uvic-auvic/Mechanical-Team/lobsta_concept_CAD/auv_assemblies/top_lid_assembly.sldasm

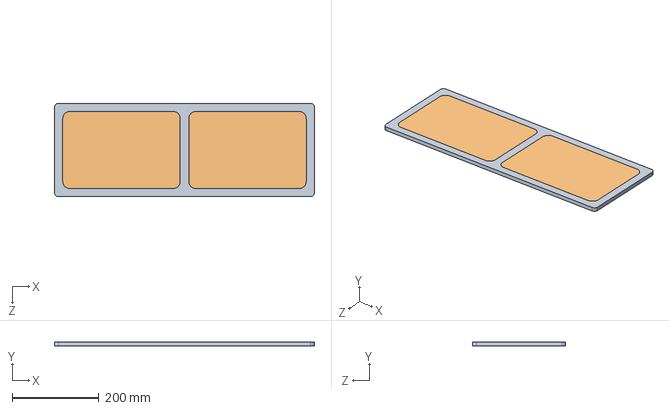
[picture p14: CAD file, 2020-06-30]
lobsta_concept_CAD/auv_assemblies/top_lid_assembly.sldasm
599.0 x 9.00 x 215.4 mm
lid_rectangular
Lid_window x 2
