uvic-auvic/Mechanical-Team/lobsta_concept_CAD/auv_assemblies/front_plate_assembly.sldasm

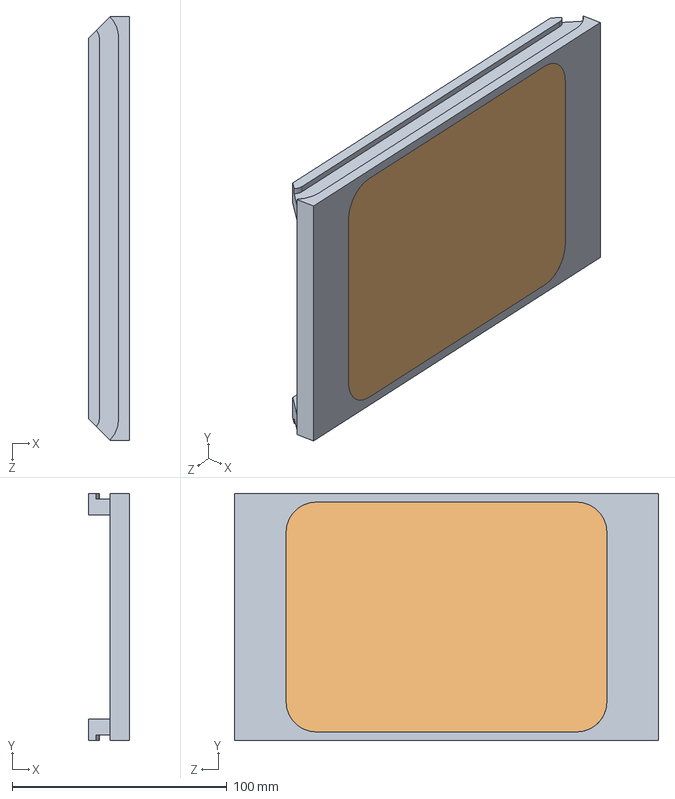
[picture p18: CAD file, 2020-06-30]
lobsta_concept_CAD/auv_assemblies/front_plate_assembly.sldasm
19.0 x 115.0 x 197.4 mm
front_plate
front_window_single
