uvic-auvic/Mechanical-Team/Final Assembly_POLARIS/Hub_bearing_assembly.SLDASM

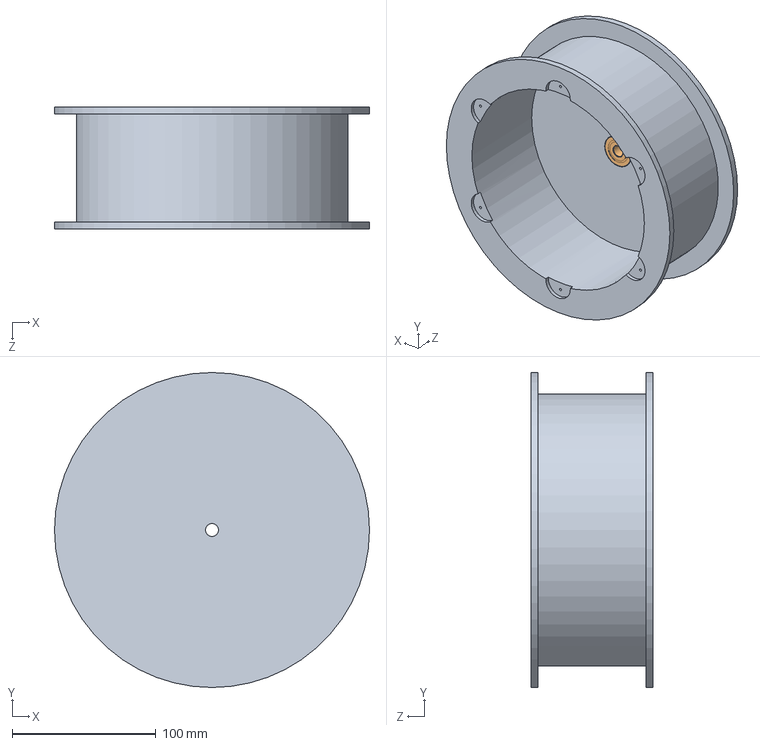
[picture p19: CAD file, 2020-06-30]
Final Assembly_POLARIS/Hub_bearing_assembly.SLDASM
219.0 x 219.0 x 85.0 mm
Hub
Outer_shaft_bearing
