uvic-auvic/Mechanical-Team/lobsta_concept_CAD/lobsta_shell_assem.SLDASM

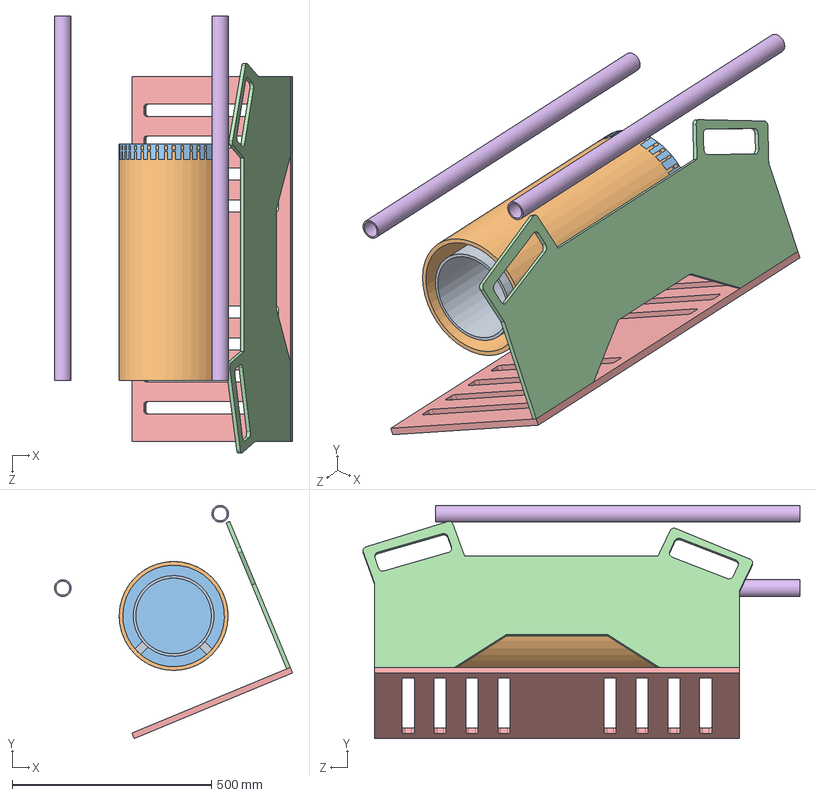
[picture p20: CAD file, 2020-01-29]
lobsta_concept_CAD/lobsta_shell_assem.SLDASM
597.3 x 584.7 x 1095.7 mm
inner_main_shell
outer_main_shell
cap
side_frame
flat_frame
Pontoon x 2
