uvic-auvic/Mechanical-Team/frame/demonstration/SubASSEM_TopBottomRail.SLDASM

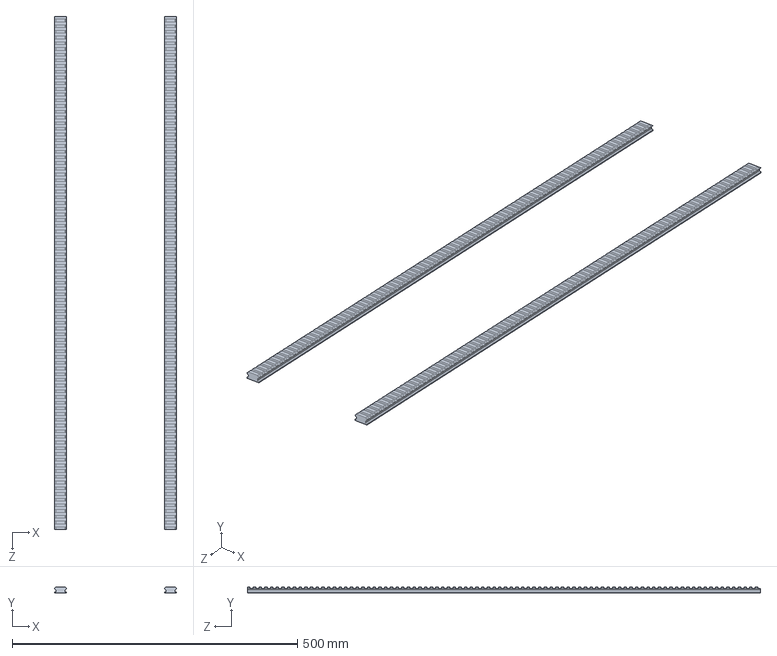
[picture p21: CAD file, 2020-06-30]
frame/demonstration/SubASSEM_TopBottomRail.SLDASM
214.0 x 11.2 x 900.0 mm
PART_PicRail x 2
