uvic-auvic/Mechanical-Team/lobsta_concept_CAD/auv_assemblies/bottom_lid_assembly.sldasm

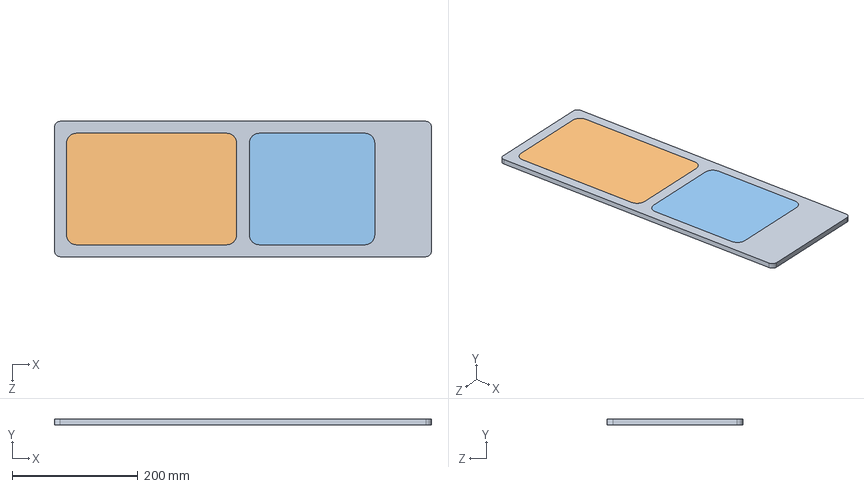
[picture p22: CAD file, 2020-06-30]
lobsta_concept_CAD/auv_assemblies/bottom_lid_assembly.sldasm
599.0 x 9.00 x 215.4 mm
lid_rectangular_bottom
Lid_window
lid_window_bottom_small
