uvic-auvic/Mechanical-Team/lobsta_concept_CAD/outer_main_shell.SLDPRT

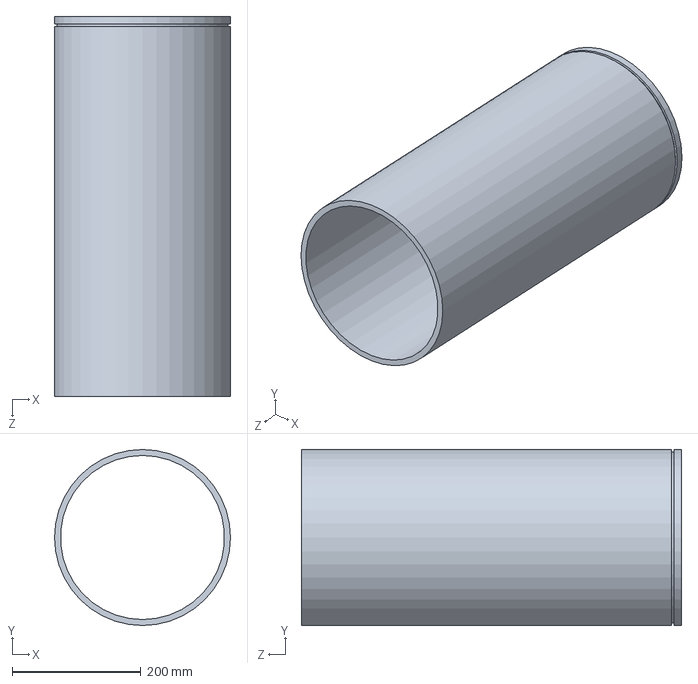
[picture p23: CAD file, 2020-01-29]
lobsta_concept_CAD/outer_main_shell.SLDPRT
273.1 x 273.1 x 590.0 mm
