uvic-auvic/Mechanical-Team/lobsta_concept_CAD/auv_assemblies/side_plate_assembly.sldasm

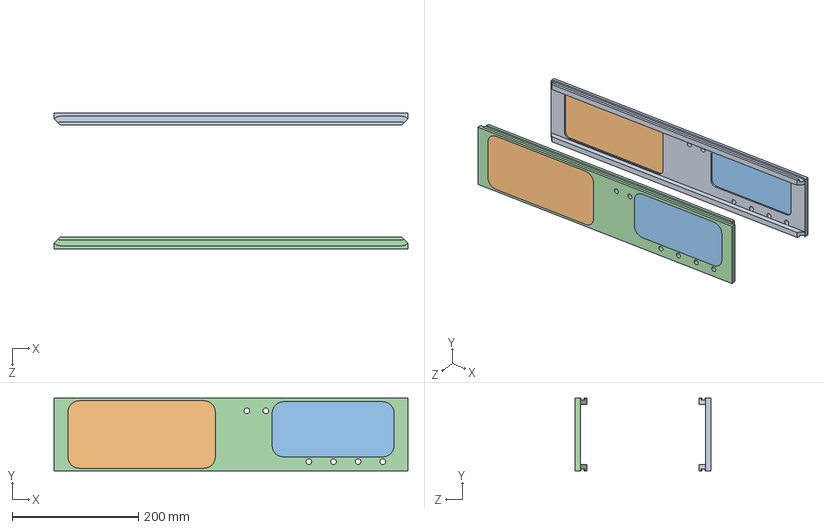
[picture p24: CAD file, 2020-05-26]
lobsta_concept_CAD/auv_assemblies/side_plate_assembly.sldasm
561.0 x 115.0 x 215.4 mm
side_plate
side_window_large x 2
side_window_small x 2
Mirrorside_plate
