uvic-auvic/Mechanical-Team/Final Assembly_POLARIS/Planet_Assembly.SLDASM

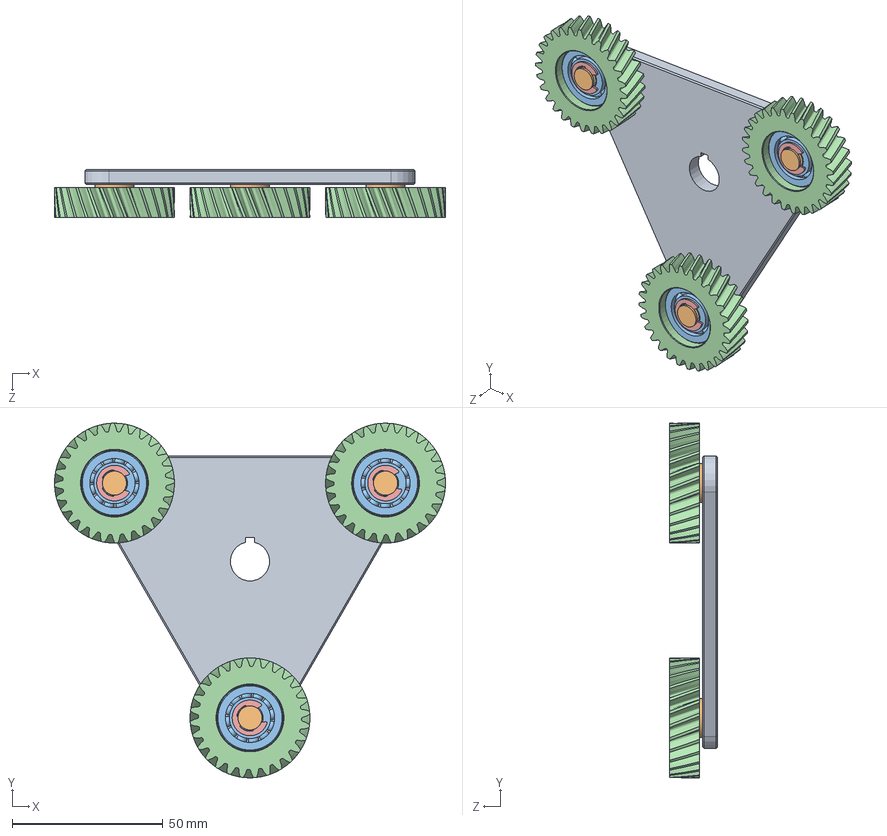
[picture p25: CAD file, 2020-06-30]
Final Assembly_POLARIS/Planet_Assembly.SLDASM
129.6 x 117.6 x 16.0 mm
Carrier
planetshaftMECH360 x 3
Planet Bearing x 3
Planet 28t x 3
98543A114_SIDE-MOUNT EXTERNAL RETAINING RING E-STYLE x 3
