uvic-auvic/Mechanical-Team/Final Assembly_POLARIS/Motor_assembly_rev1.SLDASM

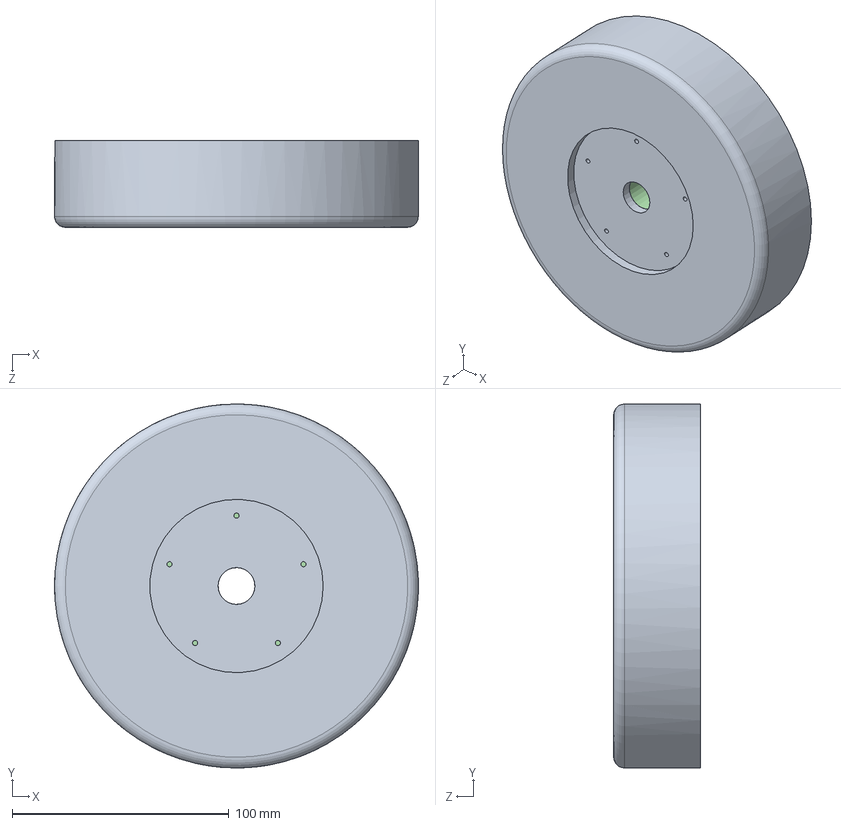
[picture p26: CAD file, 2020-06-30]
Final Assembly_POLARIS/Motor_assembly_rev1.SLDASM
168.0 x 168.0 x 40.0 mm
Motor_cover_rev1
Motor_stator
Motor_circuit_board
Motor_Rotor_rev1
