uvic-auvic/Mechanical-Team/lobsta_concept_CAD/Camera Housing/Camera_Housing_Assy.SLDASM

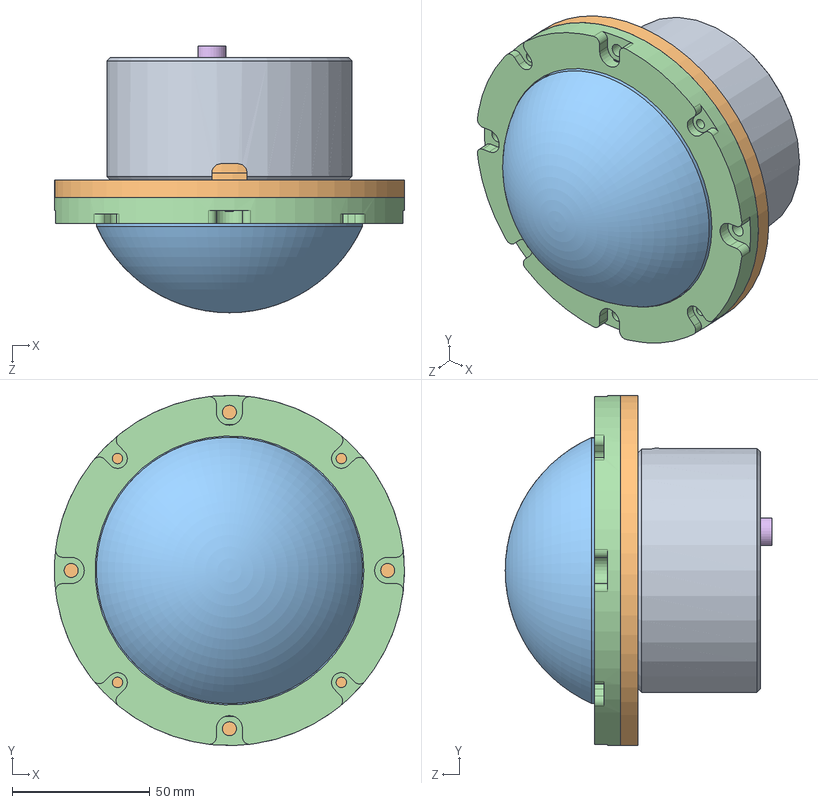
[picture p27: CAD file, 2020-03-10]
lobsta_concept_CAD/Camera Housing/Camera_Housing_Assy.SLDASM
127.0 x 127.0 x 96.7 mm
Camera_Housing
auv01_camera_hull_front_cap_videoray
auv01_camera_dome_videoray
auv01_camera_hull_lens_holder_dome_videoray
Bottom Facing Camera Mount
Maybe Screw
Test Camera (2)
Vertical Stopper
