uvic-auvic/Mechanical-Team/Final Assembly_POLARIS/Sun_Motor_Assembly.SLDASM

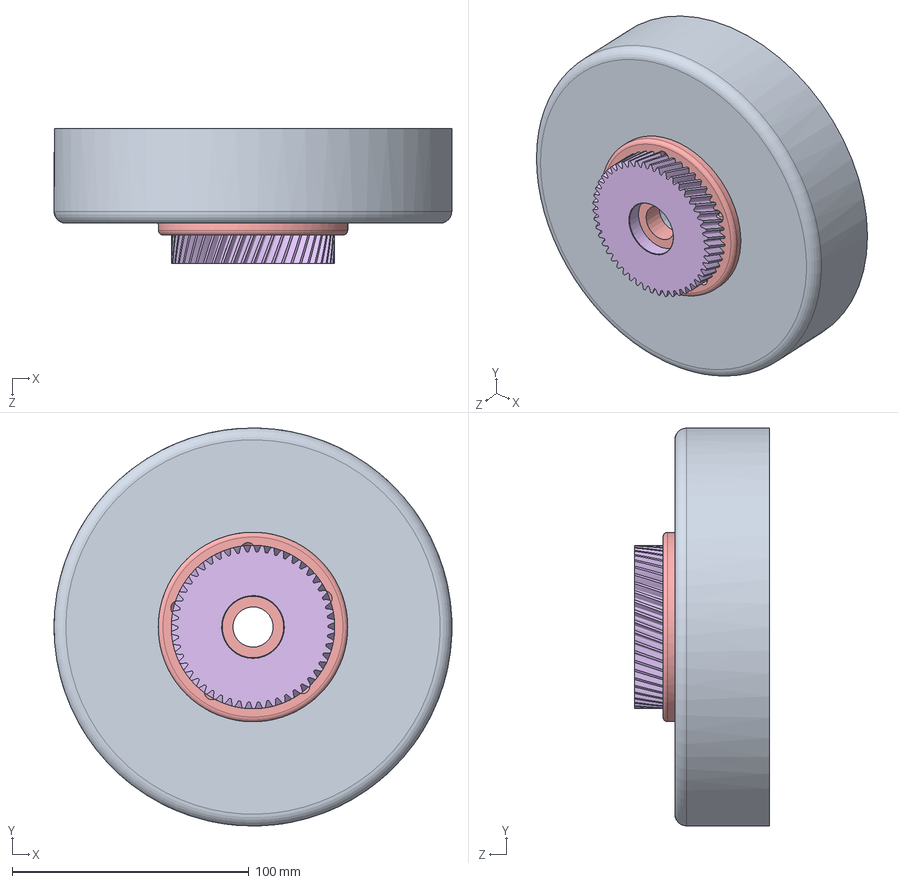
[picture p28: CAD file, 2020-06-30]
Final Assembly_POLARIS/Sun_Motor_Assembly.SLDASM
168.0 x 168.0 x 57.0 mm
Motor_cover_rev1
Motor_stator
Motor_circuit_board
Motor_Rotor_rev1
Attachment Detail
Sun 50t
