uvic-auvic/Mechanical-Team/Final Assembly_POLARIS/Sun_gear_motor_assembly.SLDASM

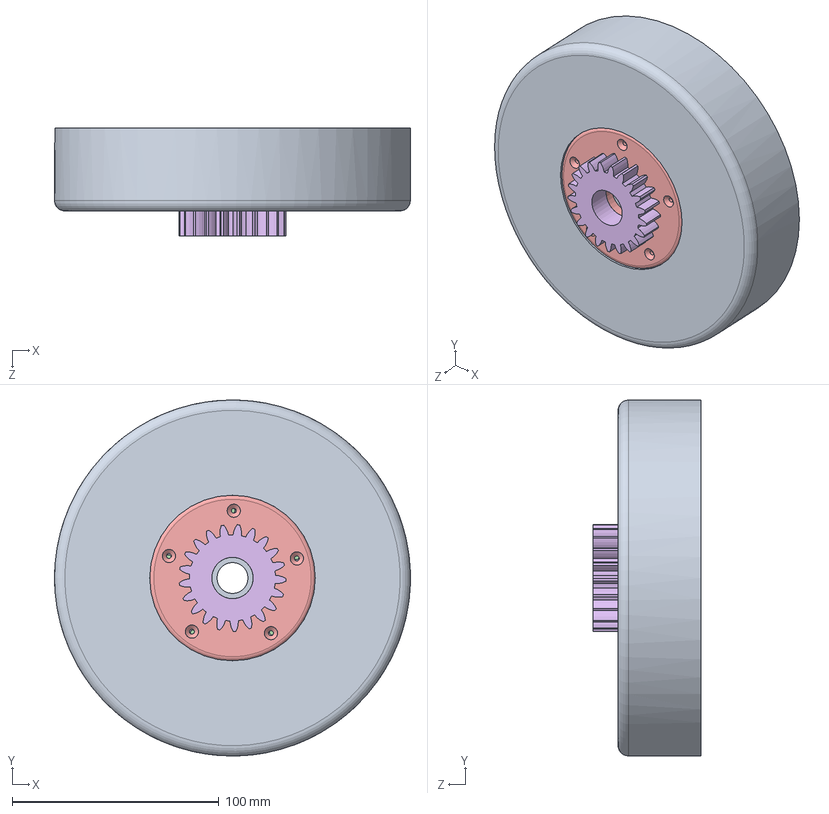
[picture p29: CAD file, 2020-06-30]
Final Assembly_POLARIS/Sun_gear_motor_assembly.SLDASM
172.0 x 172.0 x 52.0 mm
Motor_cover_rev1
Motor_stator
Motor_circuit_board
Motor_Rotor_rev1
Attachment Detail
spur gear_iso
