uvic-auvic/Mechanical-Team/Final Assembly_POLARIS/Sun Gear Attachment.SLDASM

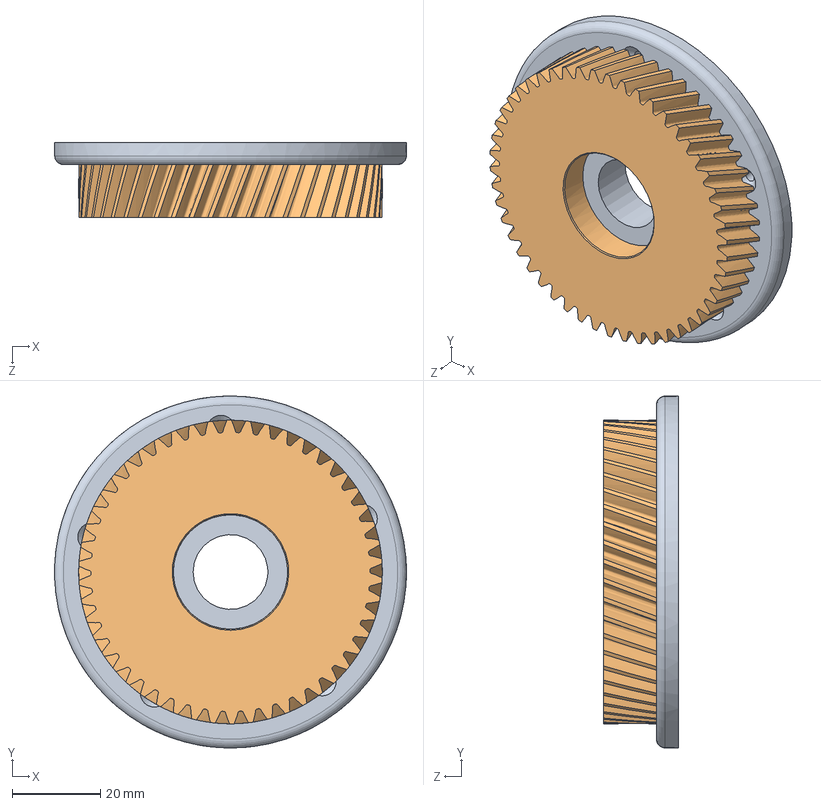
[picture p30: CAD file, 2020-06-30]
Final Assembly_POLARIS/Sun Gear Attachment.SLDASM
80.0 x 80.0 x 17.0 mm
Attachment Detail
Sun 50t
