uvic-auvic/Mechanical-Team/Final Assembly_POLARIS/Planet Gear Assembly.SLDASM

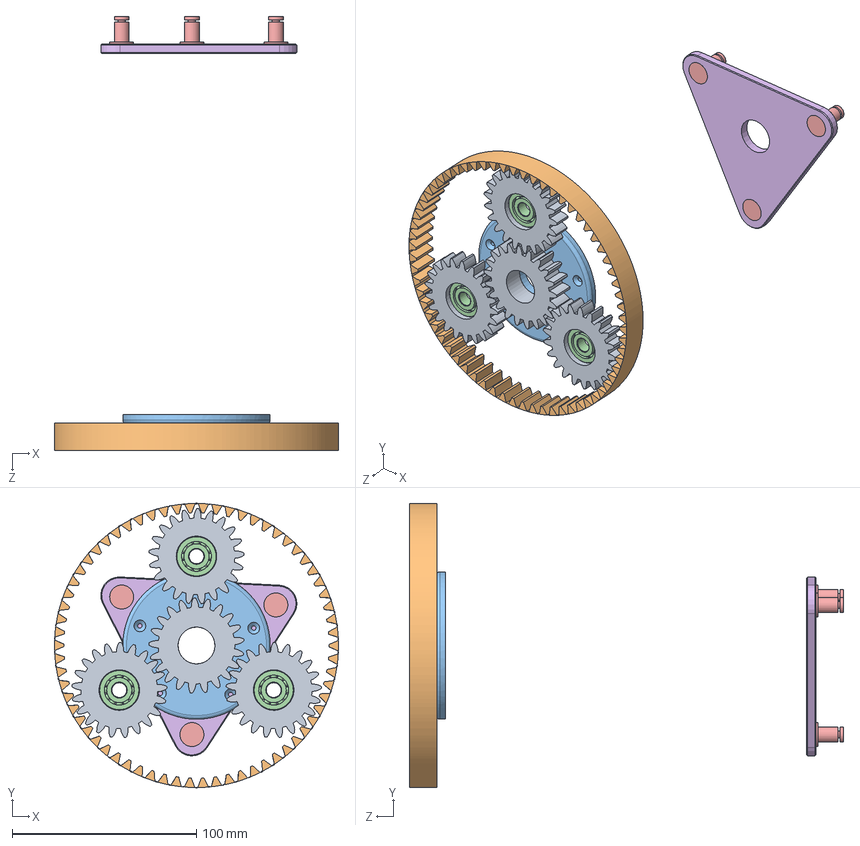
[picture p31: CAD file, 2020-06-30]
Final Assembly_POLARIS/Planet Gear Assembly.SLDASM
154.1 x 154.2 x 235.6 mm
spur gear_iso x 4
internal spur gear_iso
Attachment Detail
5972K910_BALL BEARING x 3
planetshaftMECH360 x 3
Carrier
