uvic-auvic/Mechanical-Team/Final Assembly_POLARIS/Complete_Assem.SLDASM

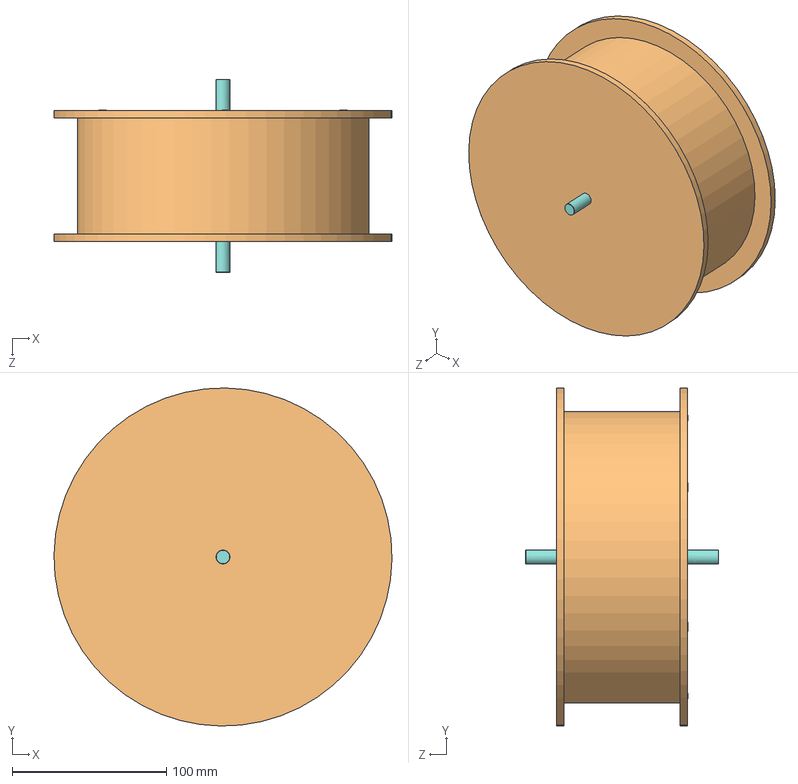
[picture p32: CAD file, 2020-06-30]
Final Assembly_POLARIS/Complete_Assem.SLDASM
219.0 x 219.0 x 125.0 mm
Carrier
planetshaftMECH360 x 3
Planet Bearing x 3
Planet 28t x 3
98543A114_SIDE-MOUNT EXTERNAL RETAINING RING E-STYLE x 3
Ring 106t Left Helix
Sun 50t
Clutch
Sun_bearing
shaftMECH360
Screws x 5
