uvic-auvic/Mechanical-Team/Blue-Robotics Mounts/Thruster Front Mount.SLDPRT

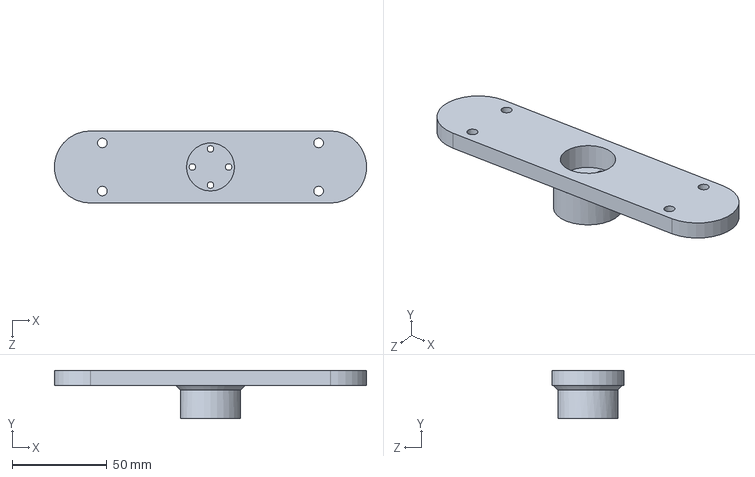
[picture p33: CAD file, 2019-07-23]
Blue-Robotics Mounts/Thruster Front Mount.SLDPRT
164.9 x 25.4 x 38.1 mm
