uvic-auvic/Mechanical-Team/Final Assembly_POLARIS/Motor_stator.SLDPRT

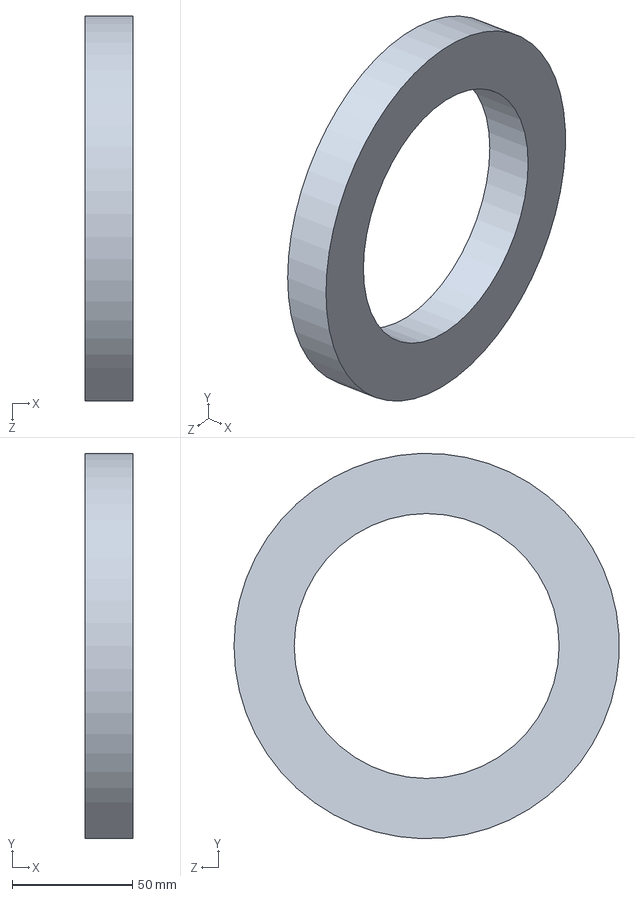
[picture p34: CAD file, 2020-06-30]
Final Assembly_POLARIS/Motor_stator.SLDPRT
20.0 x 159.9 x 159.9 mm
