uvic-auvic/Mechanical-Team/Kill Switch/top key v4.SLDPRT

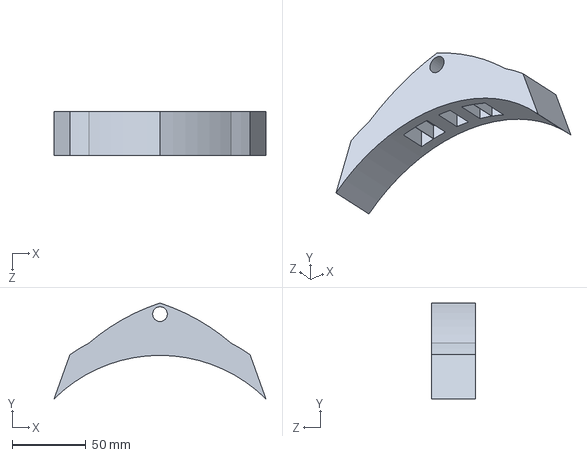
[picture p35: CAD file, 2019-07-21]
Kill Switch/top key v4.SLDPRT
143.7 x 65.1 x 30.0 mm
