uvic-auvic/Mechanical-Team/lobsta_concept_CAD/Ball Dropper/Top Bottom cap.SLDPRT

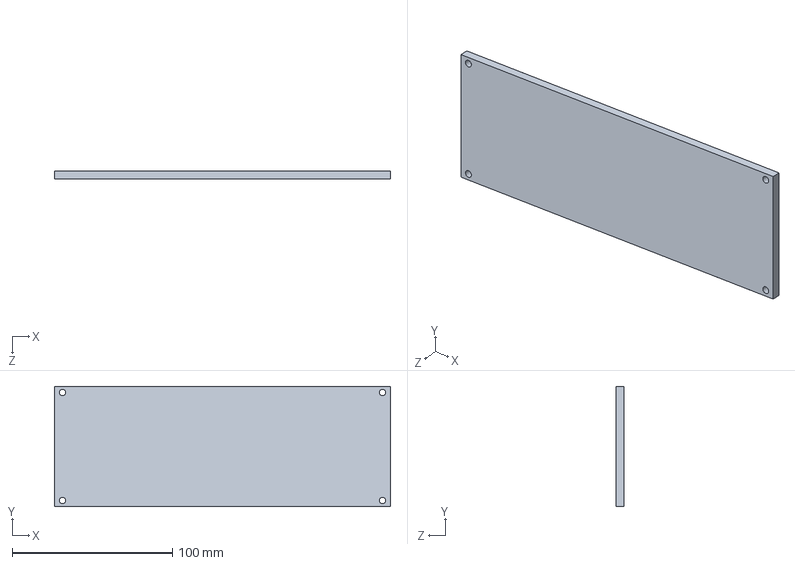
[picture p36: CAD file, 2020-06-09]
lobsta_concept_CAD/Ball Dropper/Top Bottom cap.SLDPRT
210.0 x 75.0 x 5.00 mm
