uvic-auvic/Mechanical-Team/lobsta_concept_CAD/battery assembly/cap_remove.SLDPRT

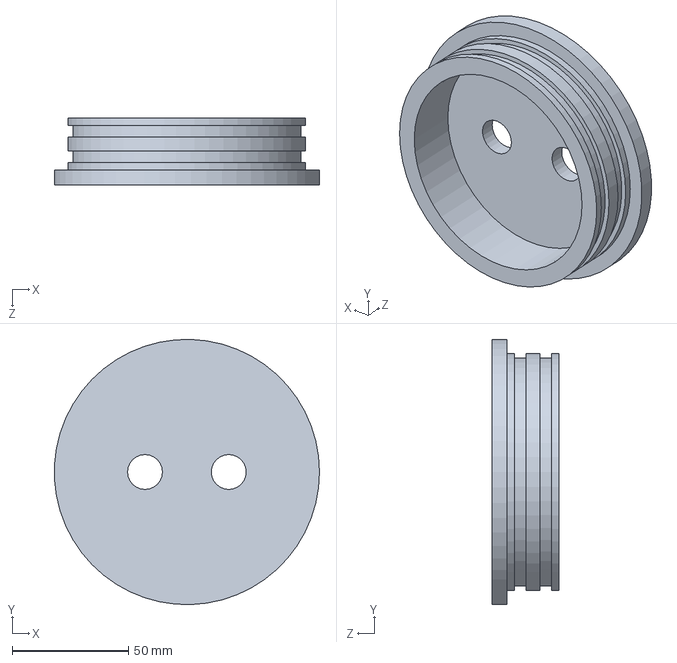
[picture p37: CAD file, 2020-02-05]
lobsta_concept_CAD/battery assembly/cap_remove.SLDPRT
113.9 x 113.9 x 28.7 mm
