uvic-auvic/Mechanical-Team/lobsta_concept_CAD/battery/XT60 Buchse.SLDPRT

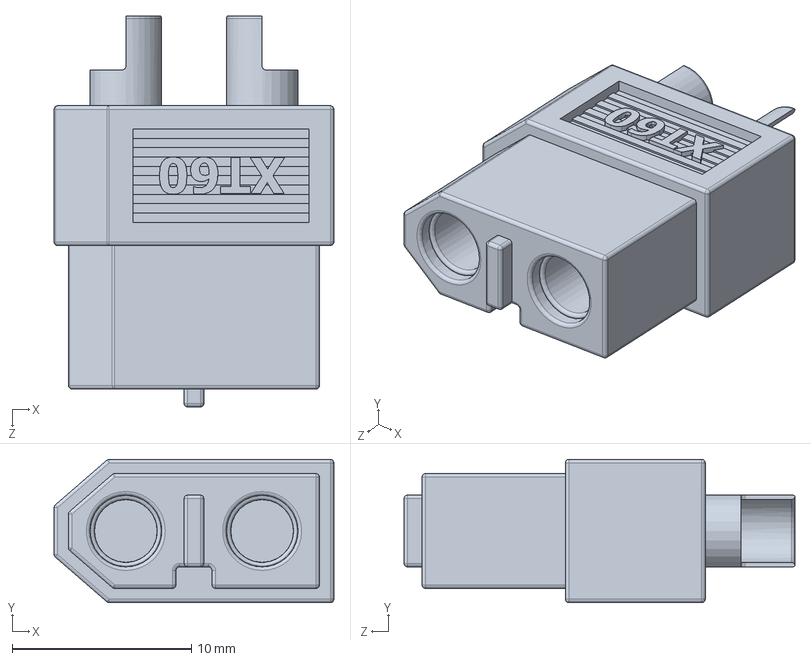
[picture p38: CAD file, 2020-03-18]
lobsta_concept_CAD/battery/XT60 Buchse.SLDPRT
15.6 x 8.00 x 21.8 mm
