uvic-auvic/Mechanical-Team/lobsta_concept_CAD/Camera Housing/Vertical Stopper.SLDPRT

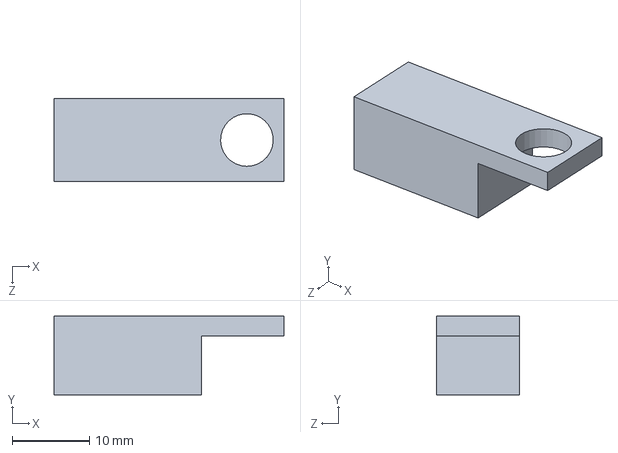
[picture p39: CAD file, 2020-03-10]
lobsta_concept_CAD/Camera Housing/Vertical Stopper.SLDPRT
29.7 x 10.2 x 10.7 mm
