uvic-auvic/Mechanical-Team/lobsta_concept_CAD/hydrophone/HydrophoneLasrecut.SLDPRT

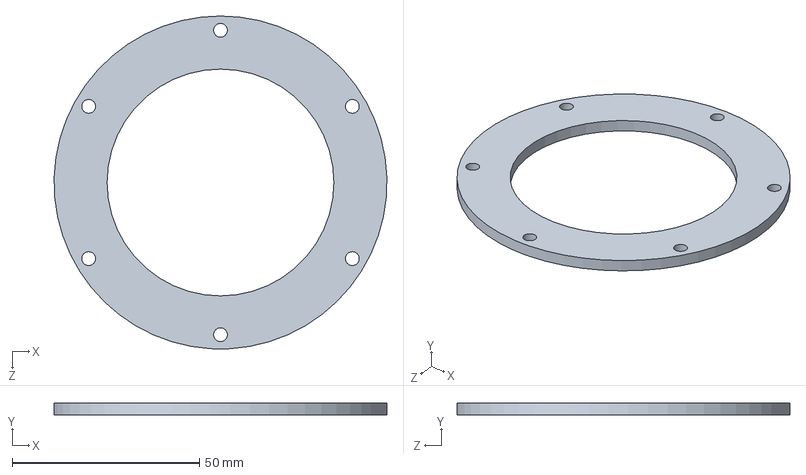
[picture p40: CAD file, 2020-06-30]
lobsta_concept_CAD/hydrophone/HydrophoneLasrecut.SLDPRT
88.9 x 3.17 x 88.9 mm
