uvic-auvic/Mechanical-Team/Mockup Drawings/square_sub/thruster.SLDPRT

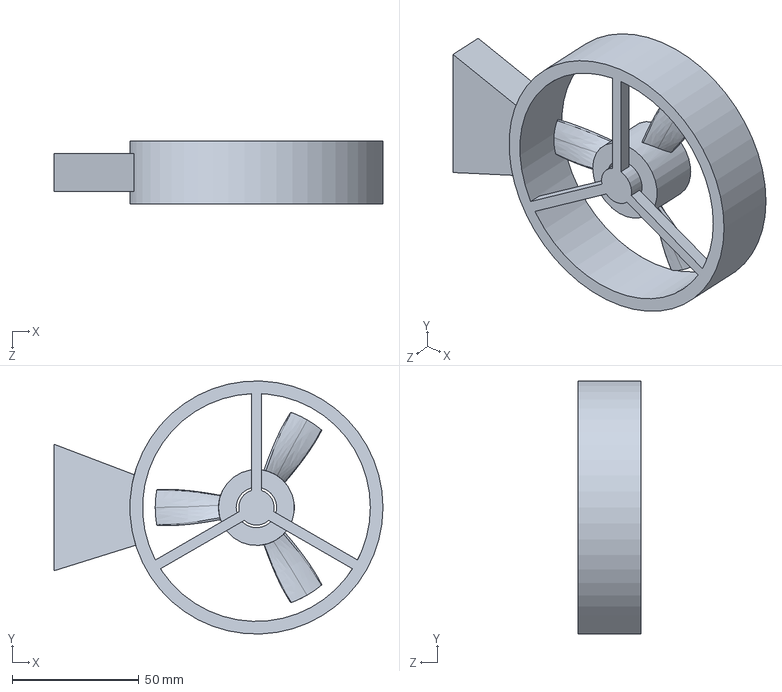
[picture p41: CAD file, 2019-10-25]
Mockup Drawings/square_sub/thruster.SLDPRT
130.0 x 99.9 x 25.0 mm
