uvic-auvic/Mechanical-Team/Torpedos/torpedo.SLDPRT

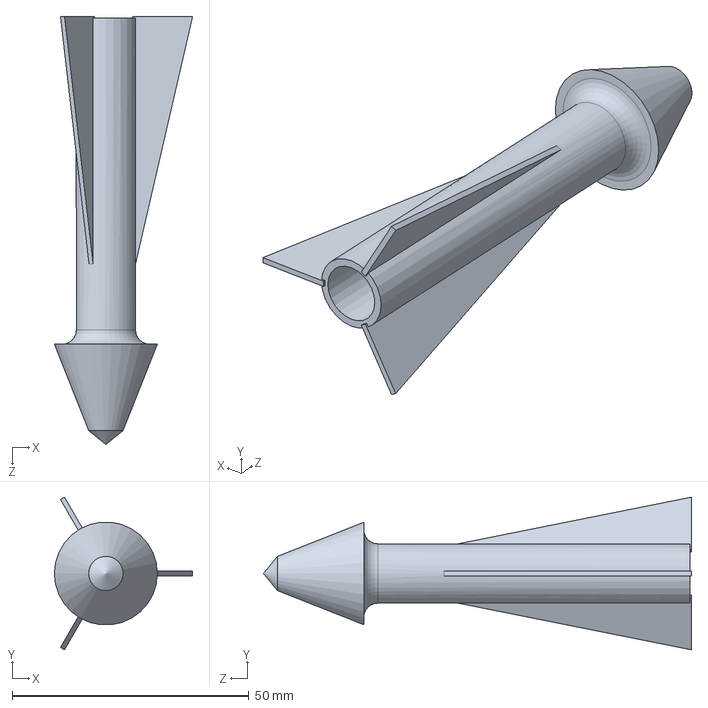
[picture p42: CAD file, 2020-06-09]
Torpedos/torpedo.SLDPRT
29.2 x 32.2 x 90.3 mm
