uvic-auvic/Mechanical-Team/Blue-Robotics Mounts/Thruster Mount.SLDPRT

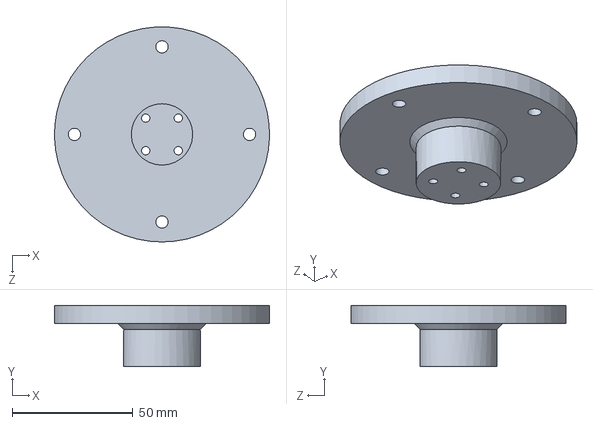
[picture p43: CAD file, 2019-07-18]
Blue-Robotics Mounts/Thruster Mount.SLDPRT
88.9 x 25.4 x 88.8 mm
