uvic-auvic/Mechanical-Team/Final Assembly_POLARIS/ShaftSleeve.SLDPRT

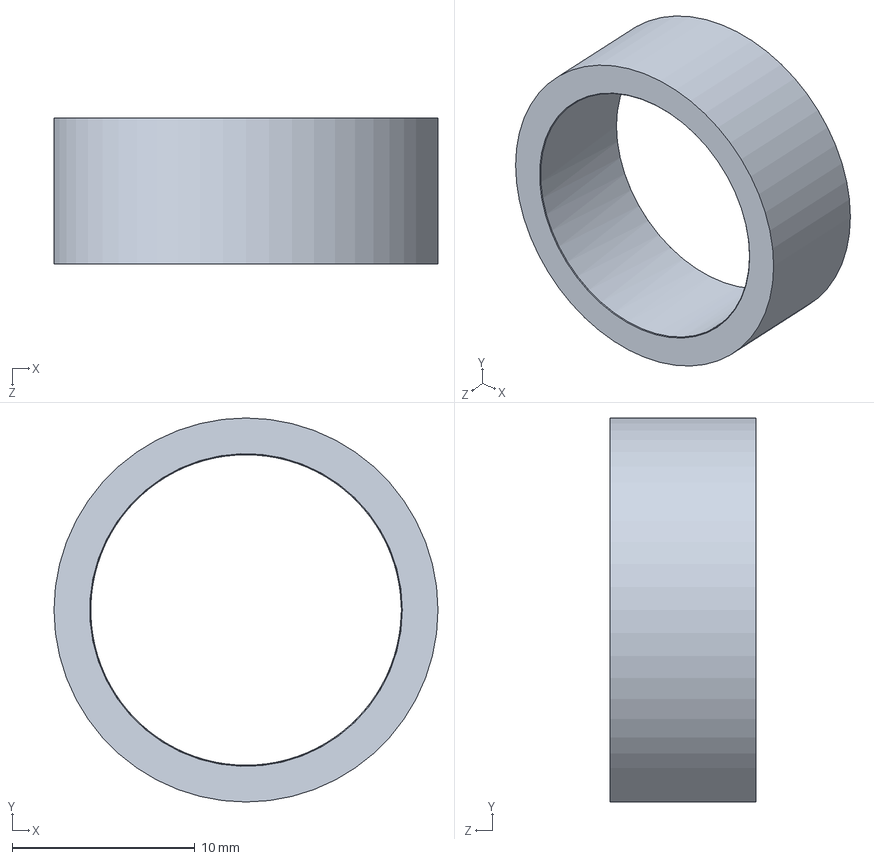
[picture p44: CAD file, 2020-06-30]
Final Assembly_POLARIS/ShaftSleeve.SLDPRT
21.0 x 21.0 x 8.00 mm
