uvic-auvic/Mechanical-Team/frame/demonstration/stand.SLDPRT

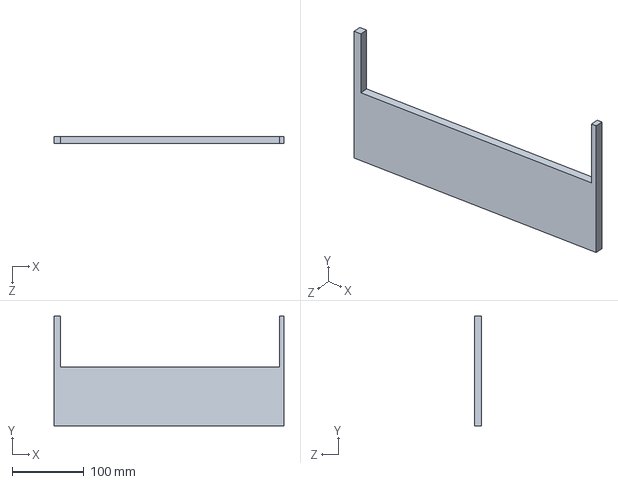
[picture p45: CAD file, 2020-06-30]
frame/demonstration/stand.SLDPRT
320.0 x 152.4 x 10.0 mm
