uvic-auvic/Mechanical-Team/Kill Switch/kill switch bottom.SLDPRT

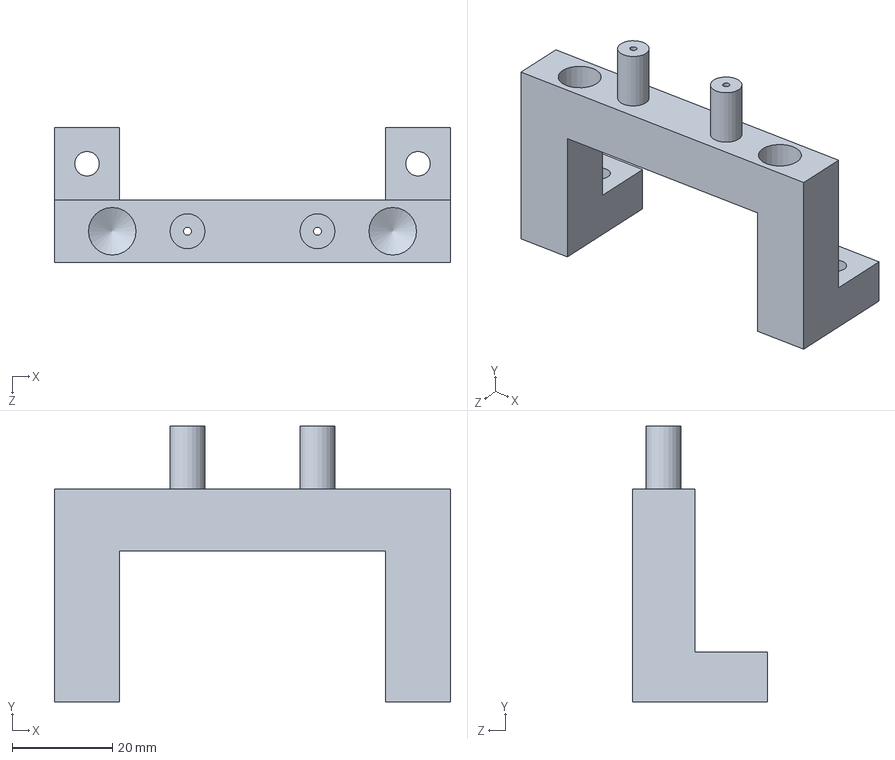
[picture p46: CAD file, 2019-07-21]
Kill Switch/kill switch bottom.SLDPRT
79.2 x 55.1 x 27.0 mm
