uvic-auvic/Mechanical-Team/lobsta_concept_CAD/auv_assemblies/front_window_single.sldprt

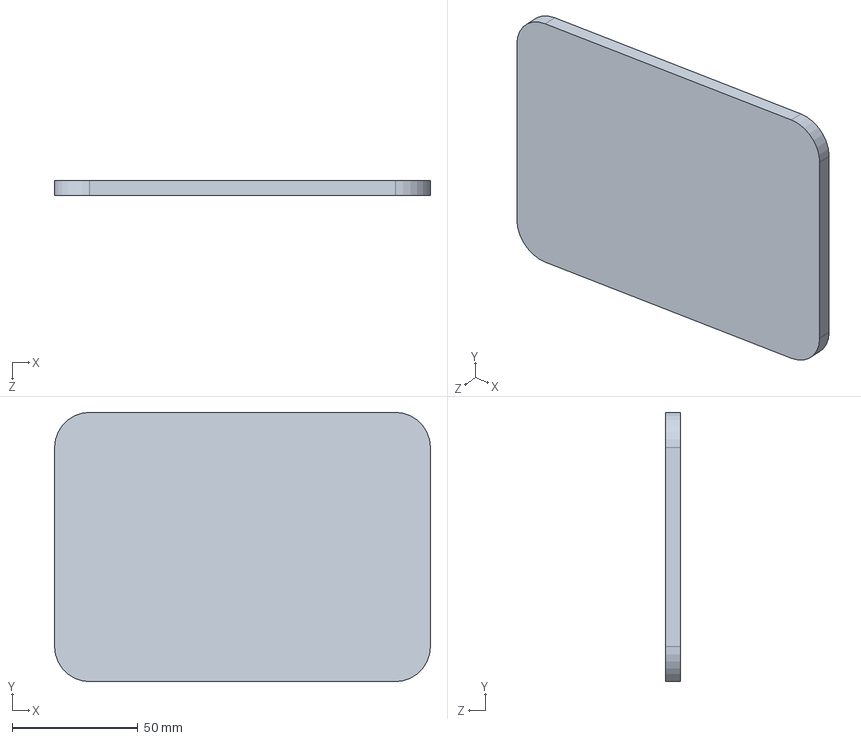
[picture p47: CAD file, 2020-06-30]
lobsta_concept_CAD/auv_assemblies/front_window_single.sldprt
149.4 x 107.0 x 6.00 mm
