uvic-auvic/Mechanical-Team/lobsta_concept_CAD/Ball Dropper/Side Plate.SLDPRT

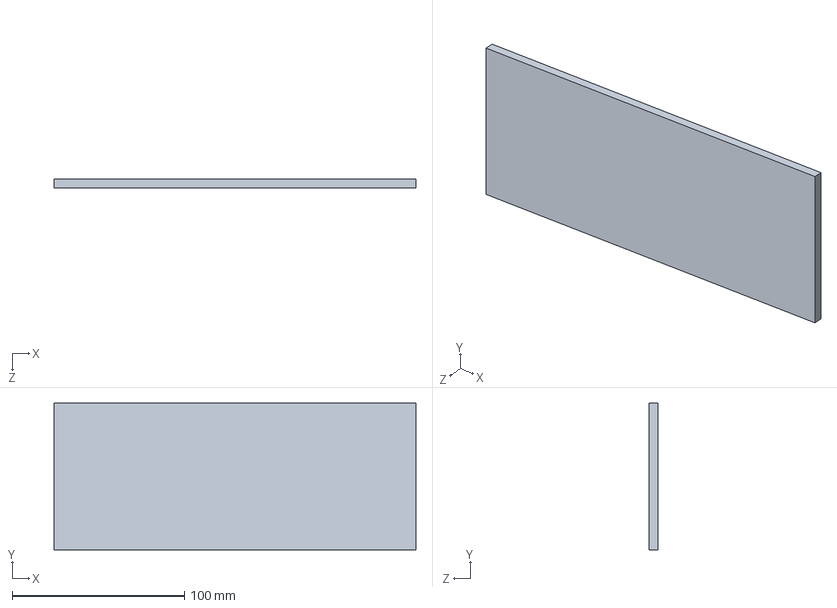
[picture p48: CAD file, 2020-06-09]
lobsta_concept_CAD/Ball Dropper/Side Plate.SLDPRT
210.0 x 85.0 x 5.00 mm
