uvic-auvic/Mechanical-Team/lobsta_concept_CAD/battery assembly/housing.SLDPRT

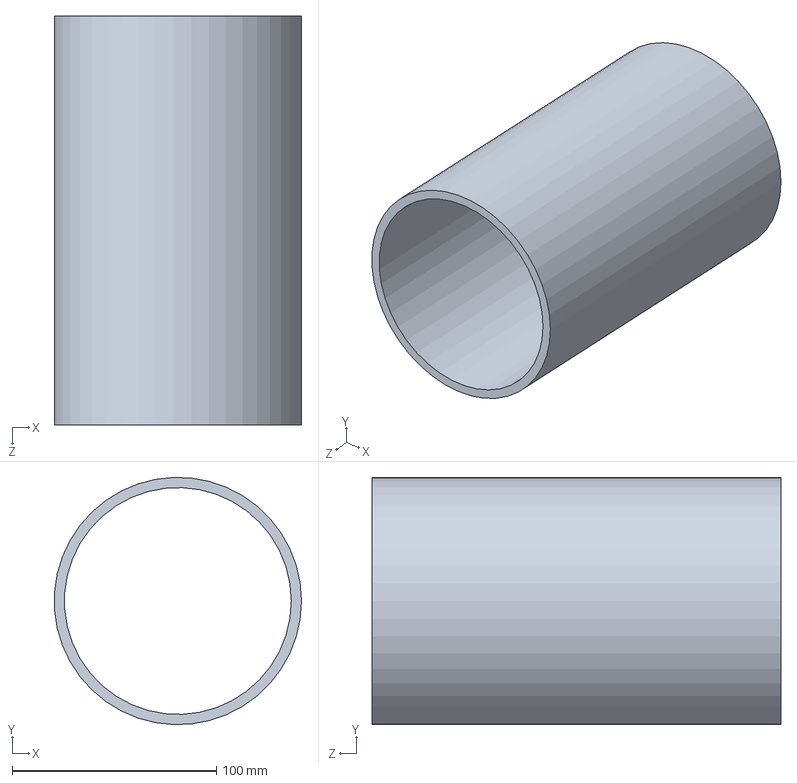
[picture p49: CAD file, 2020-02-05]
lobsta_concept_CAD/battery assembly/housing.SLDPRT
120.8 x 120.9 x 200.0 mm
