uvic-auvic/Mechanical-Team/lobsta_concept_CAD/Camera Housing/Camera_Housing.SLDPRT

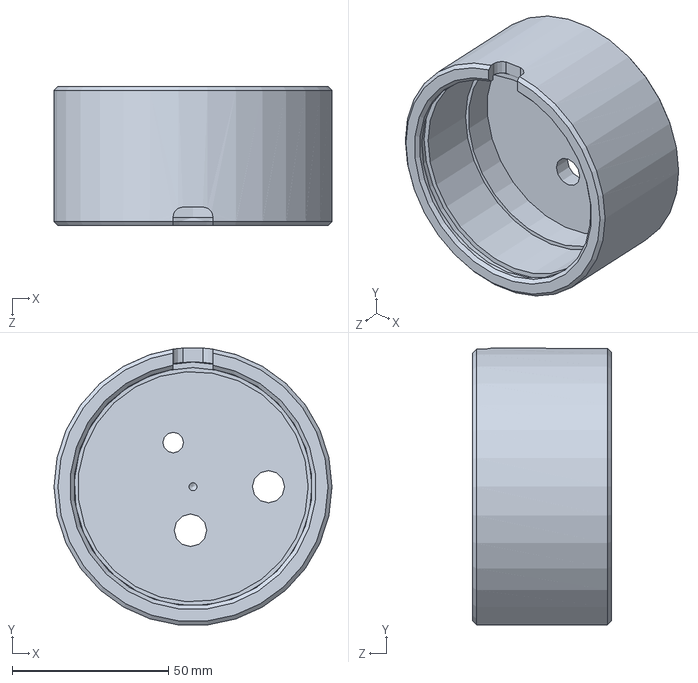
[picture p50: CAD file, 2020-03-10]
lobsta_concept_CAD/Camera Housing/Camera_Housing.SLDPRT
88.9 x 88.5 x 44.5 mm
