uvic-auvic/Mechanical-Team/lobsta_concept_CAD/end_housing.SLDPRT

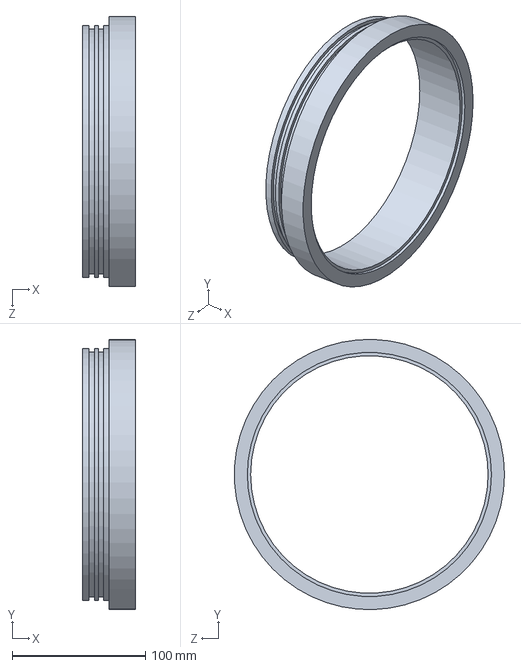
[picture p51: CAD file, 2020-02-05]
lobsta_concept_CAD/end_housing.SLDPRT
40.0 x 202.5 x 202.4 mm
