uvic-auvic/Mechanical-Team/lobsta_concept_CAD/hydrophone/HydrophoneBoard.SLDPRT

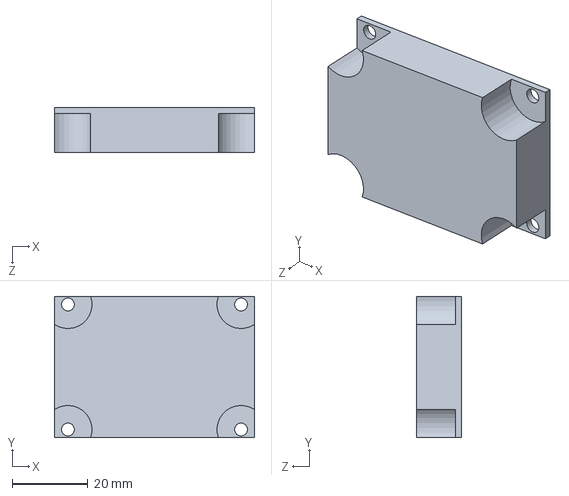
[picture p52: CAD file, 2020-03-03]
lobsta_concept_CAD/hydrophone/HydrophoneBoard.SLDPRT
52.8 x 37.3 x 11.9 mm
