uvic-auvic/Mechanical-Team/lobsta_concept_CAD/solenoid_valve/Solenoid Bracket REV2.SLDPRT

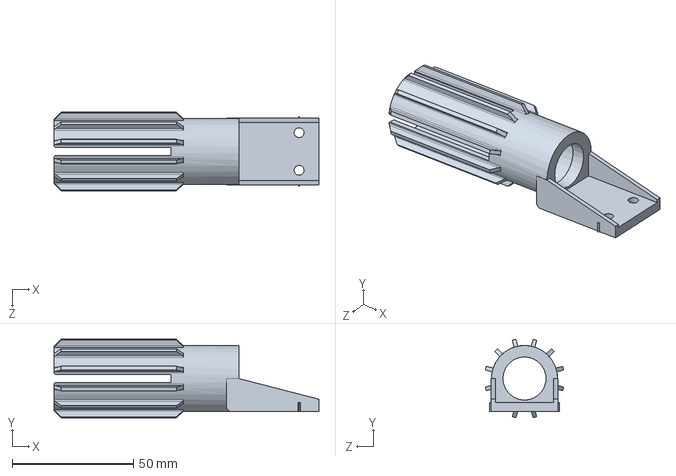
[picture p53: CAD file, 2020-02-08]
lobsta_concept_CAD/solenoid_valve/Solenoid Bracket REV2.SLDPRT
109.2 x 32.4 x 32.4 mm
