uvic-auvic/Mechanical-Team/lobsta_concept_CAD/thrusters/thruster_bracket.sldprt

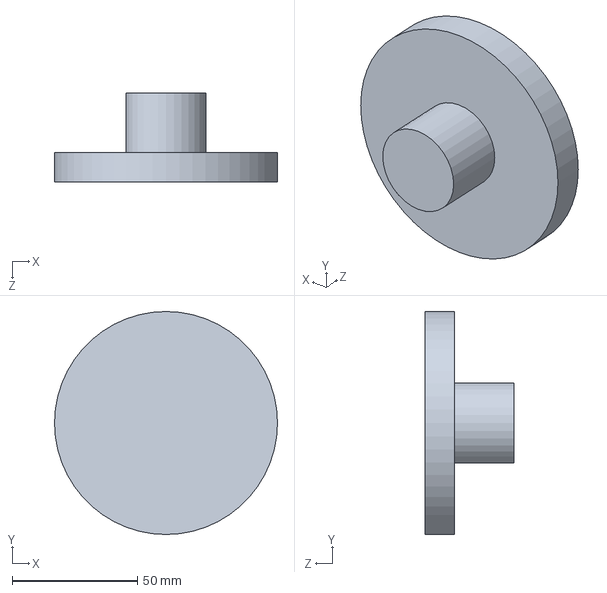
[picture p54: CAD file, 2020-03-03]
lobsta_concept_CAD/thrusters/thruster_bracket.sldprt
89.0 x 89.0 x 35.5 mm
