uvic-auvic/Mechanical-Team/lobsta_concept_CAD/usb_hub/USB-holder-box-v4.SLDPRT

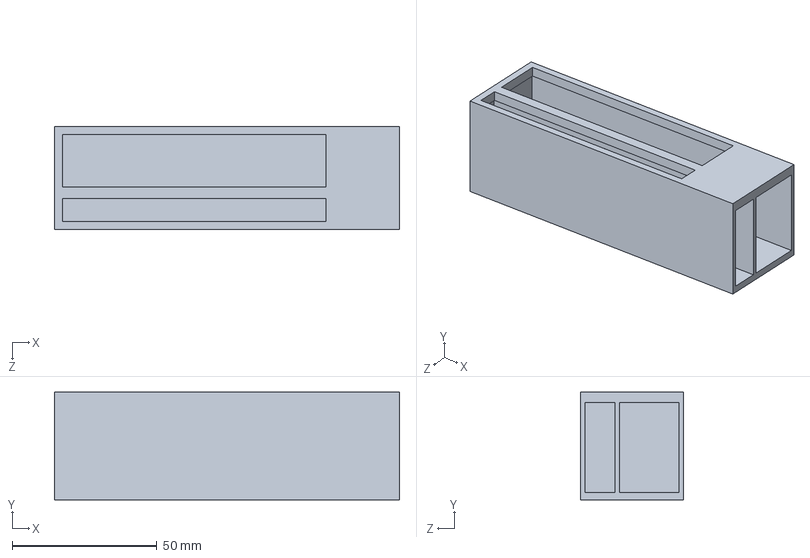
[picture p55: CAD file, 2020-03-18]
lobsta_concept_CAD/usb_hub/USB-holder-box-v4.SLDPRT
119.4 x 37.3 x 35.6 mm
