uvic-auvic/Mechanical-Team/Mockup Drawings/square_sub/side_plate.SLDPRT

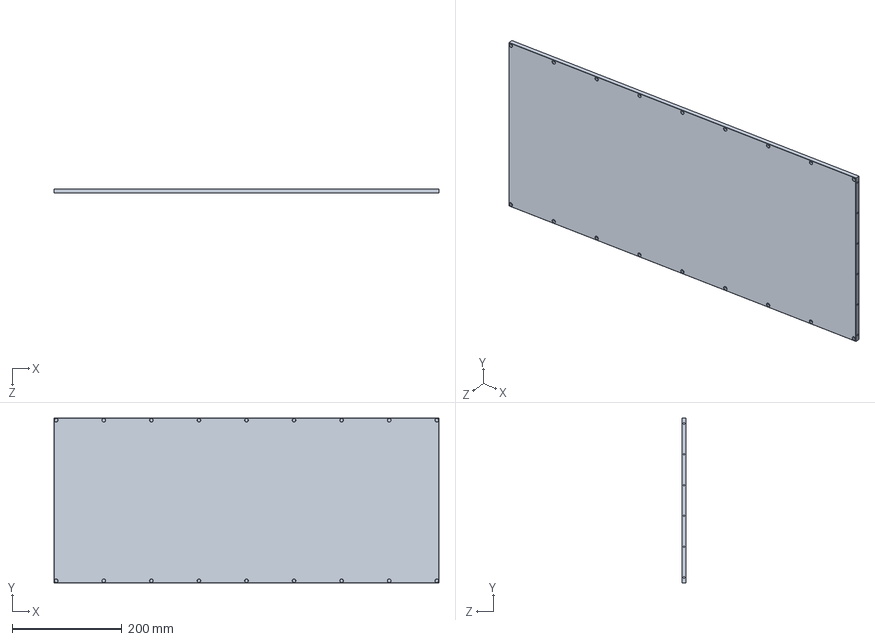
[picture p56: CAD file, 2019-10-25]
Mockup Drawings/square_sub/side_plate.SLDPRT
700.0 x 300.0 x 8.00 mm
