uvic-auvic/Mechanical-Team/Final Assembly_POLARIS/planetshaftMECH360.SLDPRT

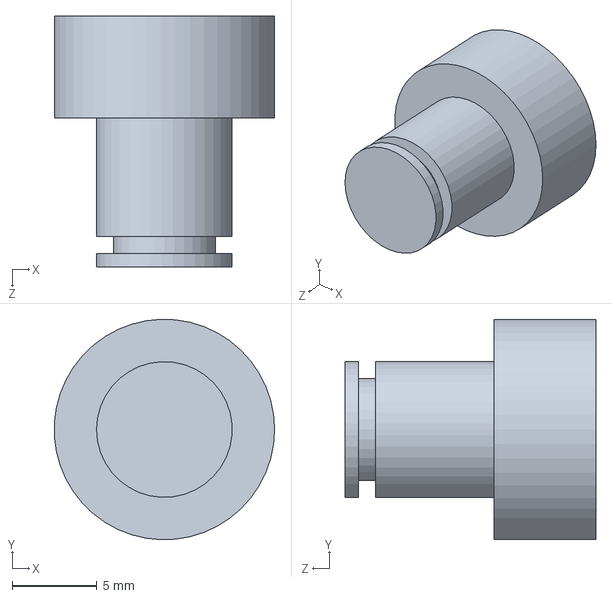
[picture p57: CAD file, 2020-06-30]
Final Assembly_POLARIS/planetshaftMECH360.SLDPRT
13.0 x 13.0 x 14.8 mm
