uvic-auvic/Mechanical-Team/lobsta_concept_CAD/battery/battery_strut.SLDPRT

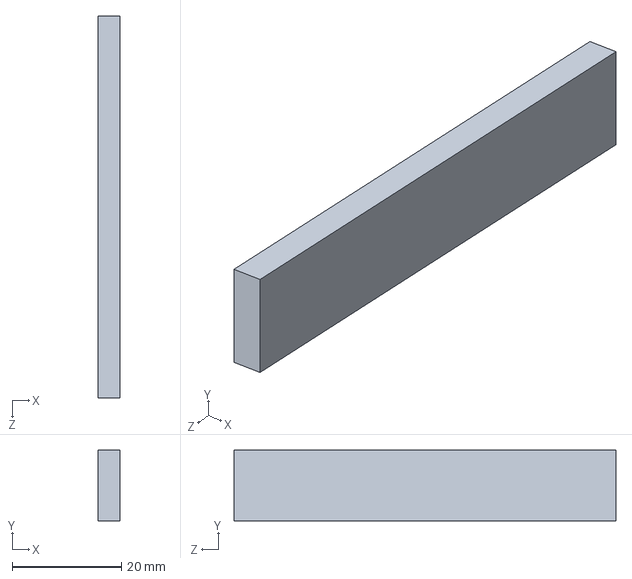
[picture p58: CAD file, 2020-03-18]
lobsta_concept_CAD/battery/battery_strut.SLDPRT
4.00 x 13.0 x 70.0 mm
