uvic-auvic/Mechanical-Team/lobsta_concept_CAD/Camera Housing/auv01_camera_hull_front_cap_videoray.SLDPRT

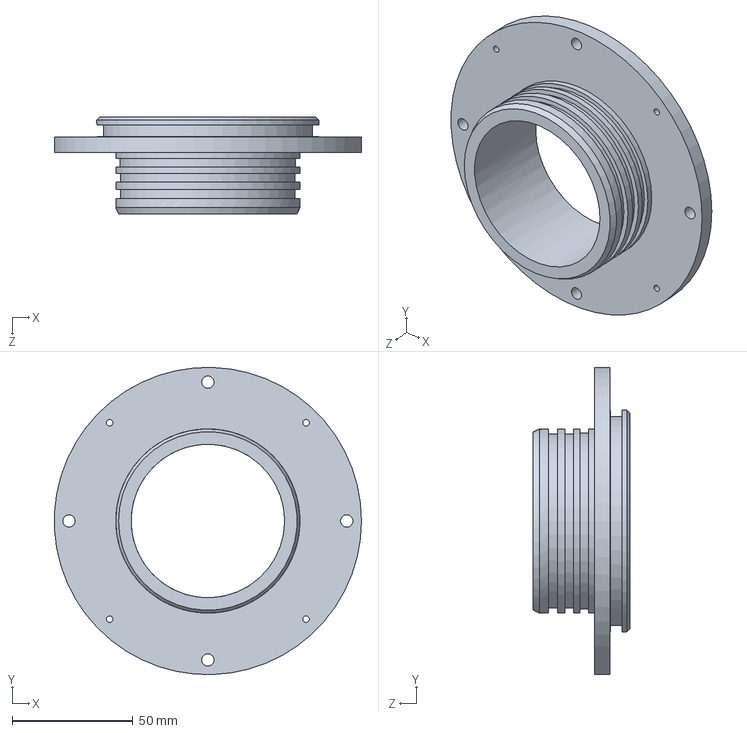
[picture p59: CAD file, 2020-03-10]
lobsta_concept_CAD/Camera Housing/auv01_camera_hull_front_cap_videoray.SLDPRT
126.9 x 126.9 x 40.0 mm
