uvic-auvic/Mechanical-Team/lobsta_concept_CAD/hydrophone/HydrophoneMount.SLDPRT

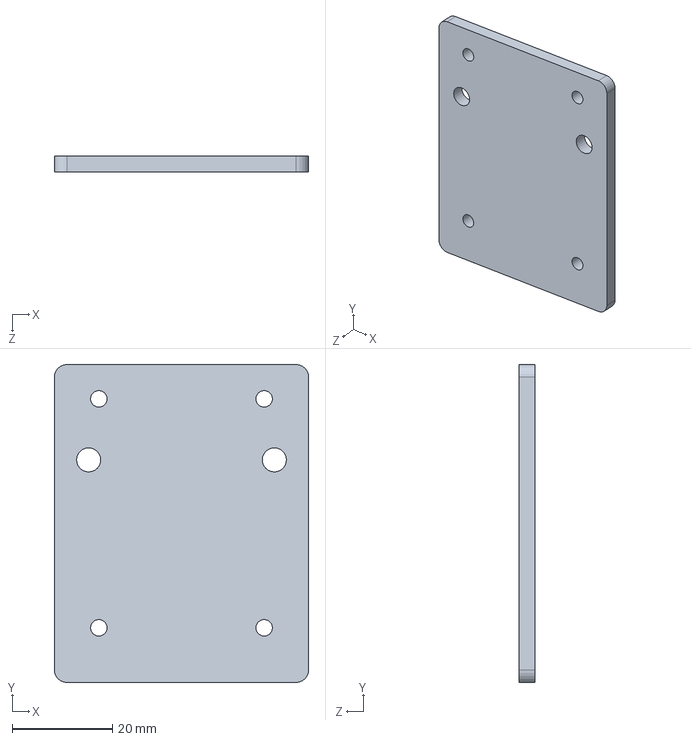
[picture p60: CAD file, 2020-03-03]
lobsta_concept_CAD/hydrophone/HydrophoneMount.SLDPRT
50.8 x 63.5 x 3.17 mm
