uvic-auvic/Mechanical-Team/lobsta_concept_CAD/Pontoon.SLDPRT

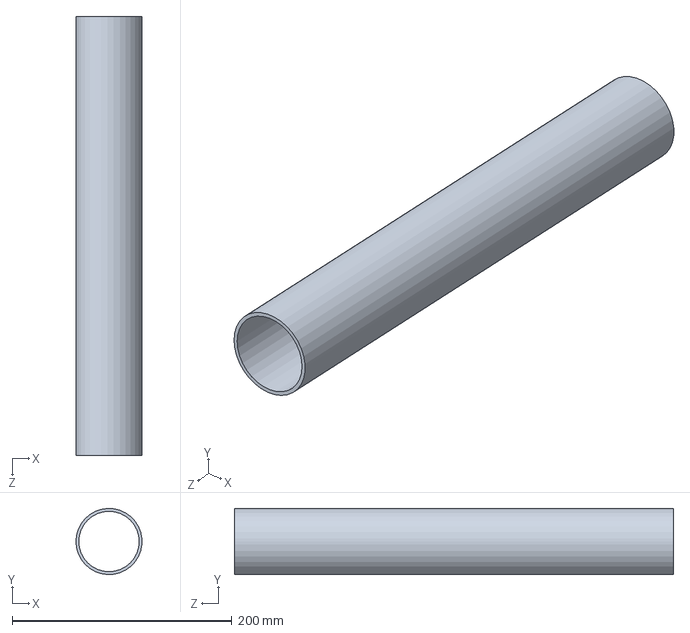
[picture p61: CAD file, 2020-02-05]
lobsta_concept_CAD/Pontoon.SLDPRT
60.3 x 60.2 x 400.0 mm
