uvic-auvic/Mechanical-Team/lobsta_concept_CAD/solenoid_valve/Solenoid Valve bottom REV1.SLDPRT

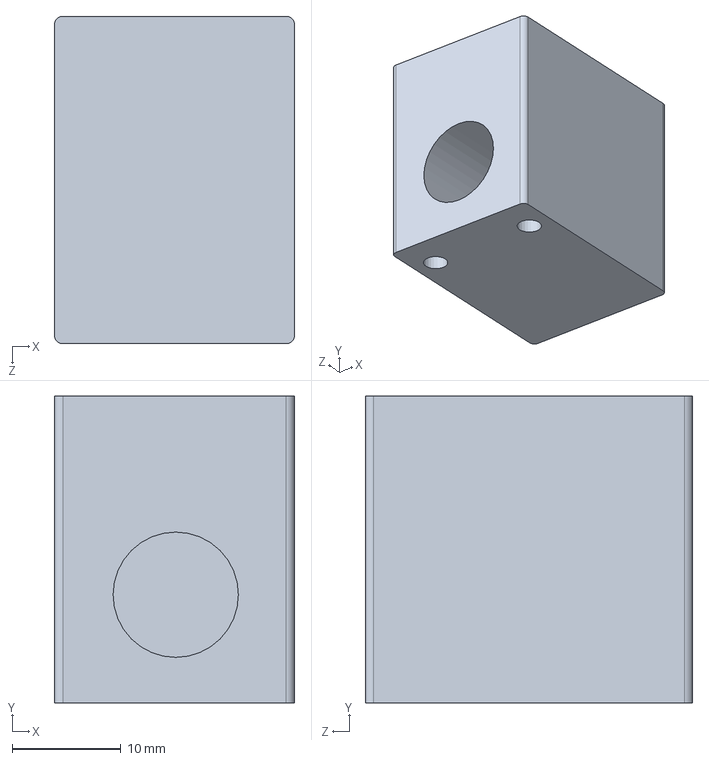
[picture p62: CAD file, 2020-02-08]
lobsta_concept_CAD/solenoid_valve/Solenoid Valve bottom REV1.SLDPRT
22.0 x 28.2 x 30.1 mm
