uvic-auvic/Mechanical-Team/Mockup Drawings/square_sub/back_plate.SLDPRT

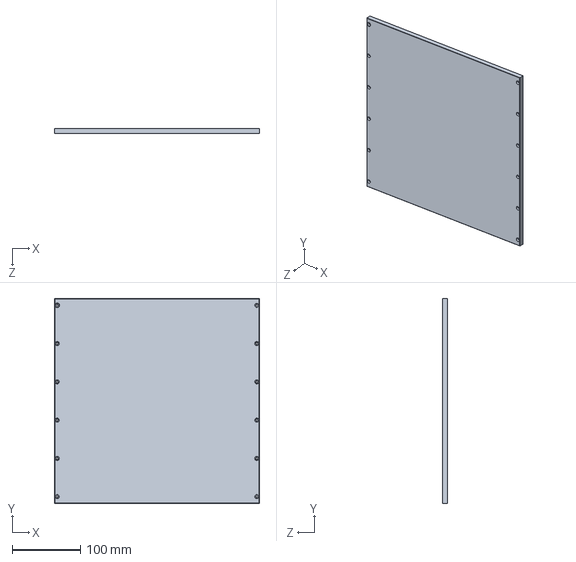
[picture p63: CAD file, 2019-10-25]
Mockup Drawings/square_sub/back_plate.SLDPRT
300.0 x 300.0 x 8.00 mm
