uvic-auvic/Mechanical-Team/Torpedos/gattling disk.SLDPRT

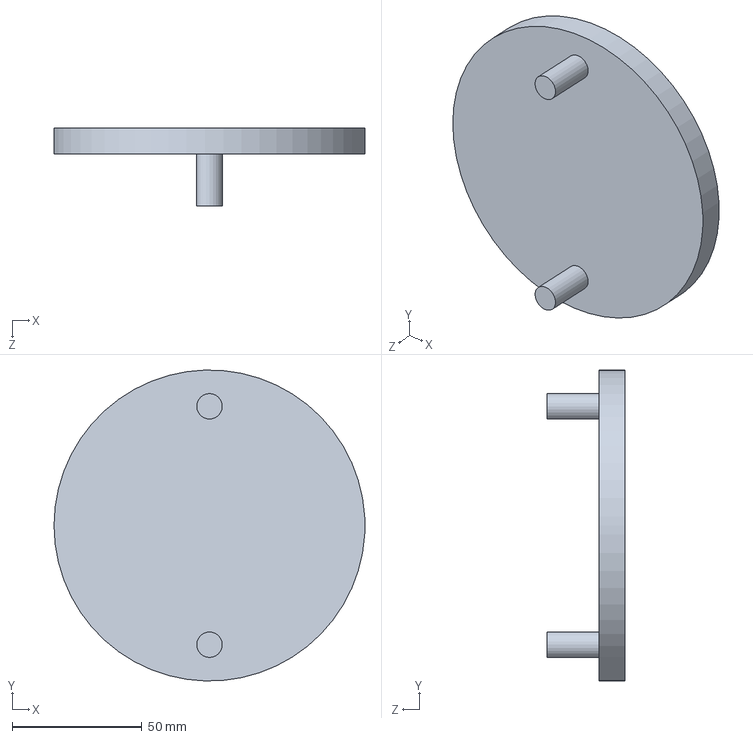
[picture p64: CAD file, 2020-06-09]
Torpedos/gattling disk.SLDPRT
120.0 x 119.9 x 30.0 mm
