uvic-auvic/Mechanical-Team/lobsta_concept_CAD/Ball Dropper/Back Plate.SLDPRT

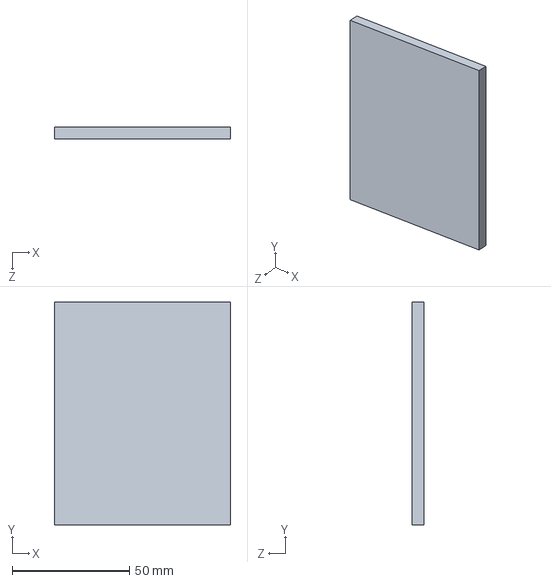
[picture p65: CAD file, 2020-06-09]
lobsta_concept_CAD/Ball Dropper/Back Plate.SLDPRT
75.0 x 95.0 x 5.00 mm
