uvic-auvic/Mechanical-Team/lobsta_concept_CAD/battery assembly/cap_fixed.SLDPRT

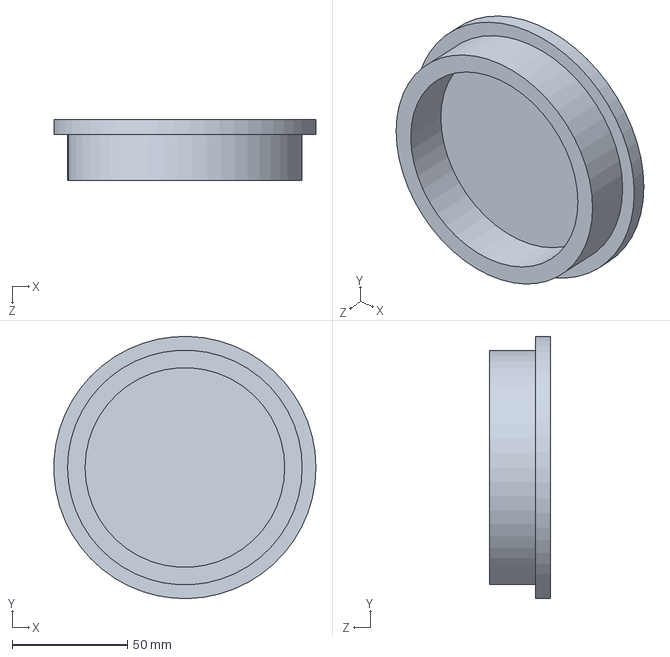
[picture p66: CAD file, 2020-02-05]
lobsta_concept_CAD/battery assembly/cap_fixed.SLDPRT
113.9 x 113.9 x 26.4 mm
