uvic-auvic/Mechanical-Team/lobsta_concept_CAD/battery/Multistar_3000mAh_4S_Lipo_Battery.SLDPRT

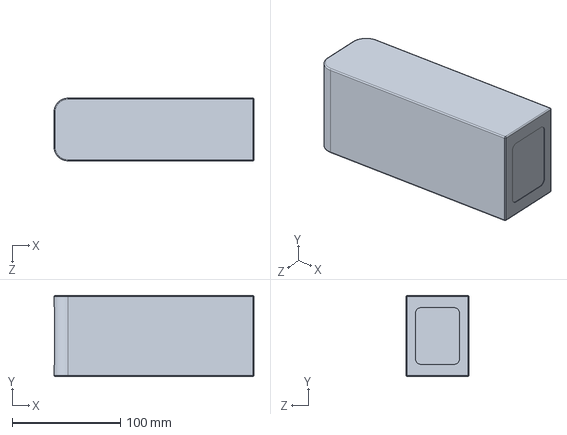
[picture p67: CAD file, 2020-03-10]
lobsta_concept_CAD/battery/Multistar_3000mAh_4S_Lipo_Battery.SLDPRT
185.0 x 75.0 x 58.0 mm
