uvic-auvic/Mechanical-Team/lobsta_concept_CAD/Camera Housing/Bottom Facing Camera Mount.SLDPRT

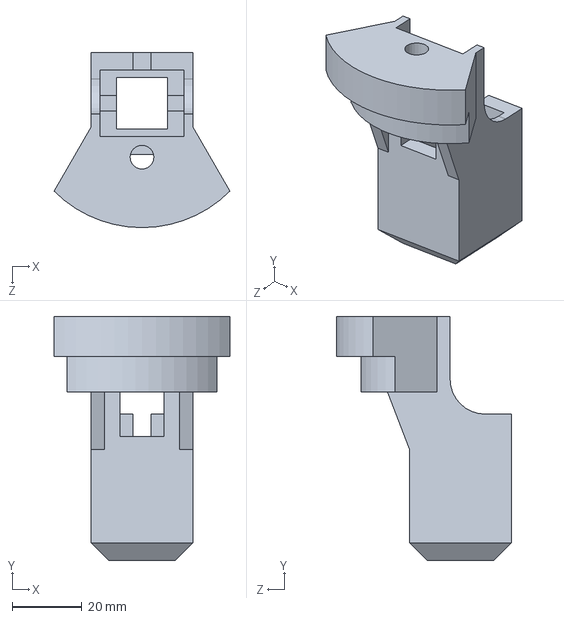
[picture p68: CAD file, 2020-03-10]
lobsta_concept_CAD/Camera Housing/Bottom Facing Camera Mount.SLDPRT
50.3 x 69.8 x 50.2 mm
