uvic-auvic/Mechanical-Team/lobsta_concept_CAD/end_cap.SLDPRT

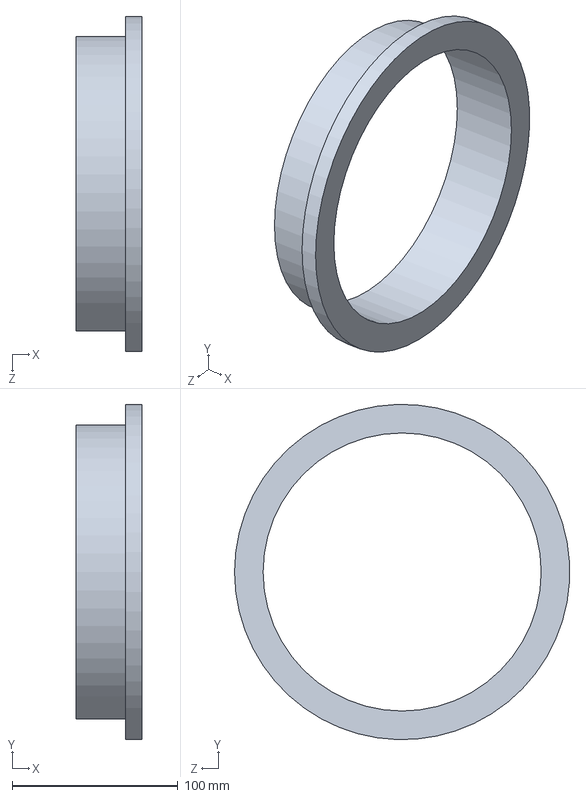
[picture p69: CAD file, 2020-02-05]
lobsta_concept_CAD/end_cap.SLDPRT
40.0 x 202.5 x 202.4 mm
