uvic-auvic/Mechanical-Team/lobsta_concept_CAD/hydrophone/Hydrophone.SLDPRT

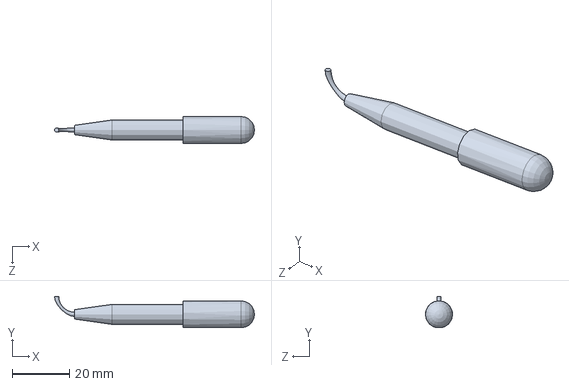
[picture p70: CAD file, 2020-03-03]
lobsta_concept_CAD/hydrophone/Hydrophone.SLDPRT
70.1 x 11.0 x 9.47 mm
