uvic-auvic/Mechanical-Team/lobsta_concept_CAD/solenoid_valve/Solenoid Valve Top REV1.SLDPRT

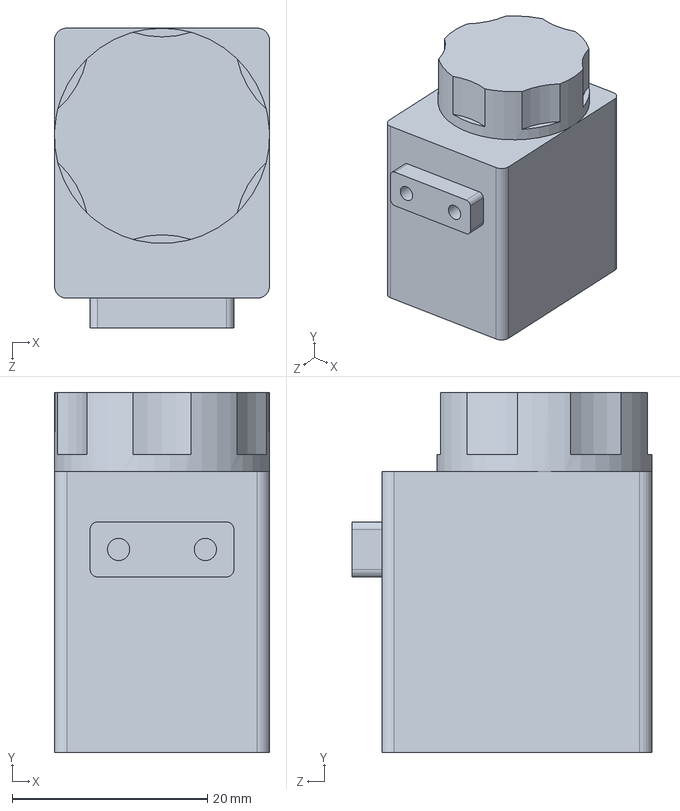
[picture p71: CAD file, 2020-02-08]
lobsta_concept_CAD/solenoid_valve/Solenoid Valve Top REV1.SLDPRT
22.0 x 36.9 x 30.7 mm
