uvic-auvic/Mechanical-Team/Torpedos/gattling_stand.SLDPRT

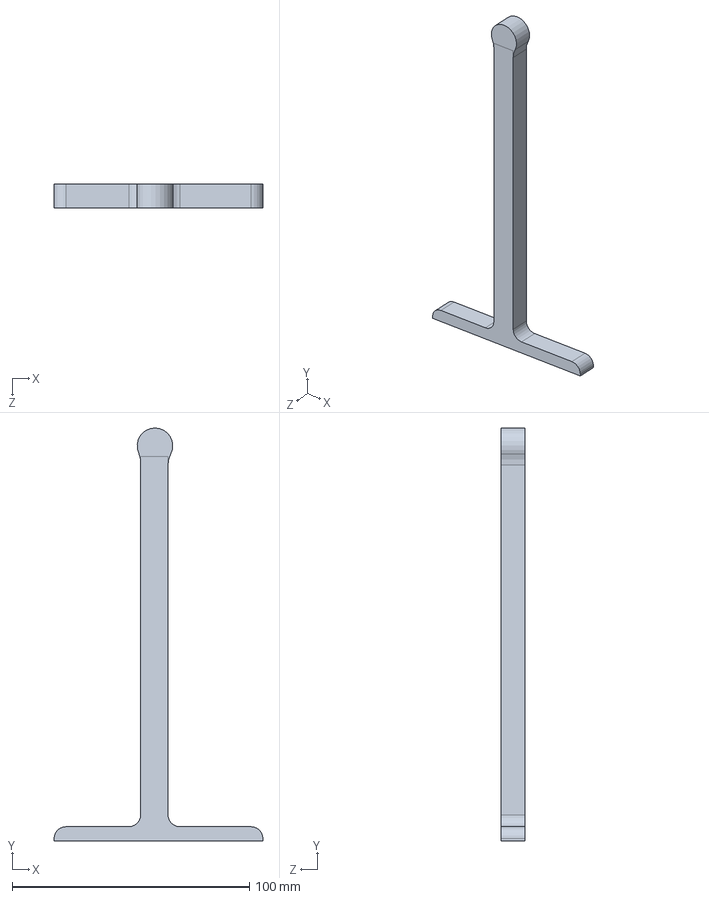
[picture p72: CAD file, 2020-06-09]
Torpedos/gattling_stand.SLDPRT
88.0 x 174.0 x 10.0 mm
