uvic-auvic/Mechanical-Team/Final Assembly_POLARIS/Outer_shaft_bearing.SLDPRT

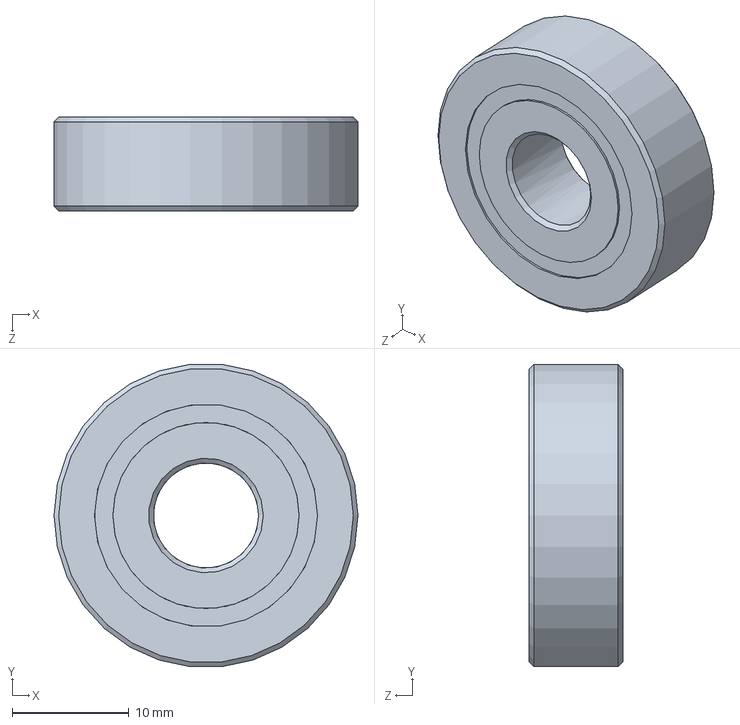
[picture p73: CAD file, 2020-06-30]
Final Assembly_POLARIS/Outer_shaft_bearing.SLDPRT
26.0 x 25.9 x 8.00 mm
