uvic-auvic/Mechanical-Team/frame/demonstration/PART_PeriphMount.SLDPRT

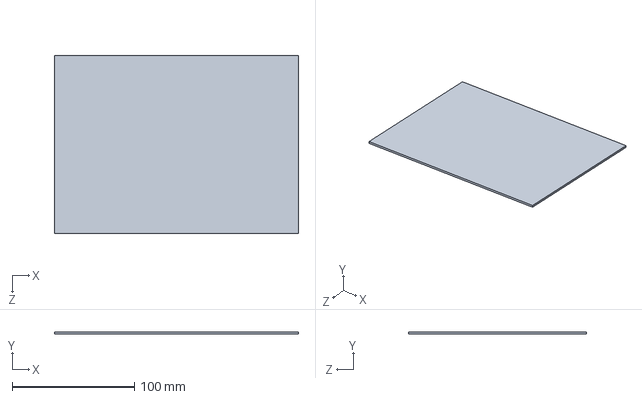
[picture p74: CAD file, 2020-06-30]
frame/demonstration/PART_PeriphMount.SLDPRT
200.0 x 2.00 x 146.3 mm
