uvic-auvic/Mechanical-Team/lobsta_concept_CAD/Ball Dropper/BALL.SLDPRT

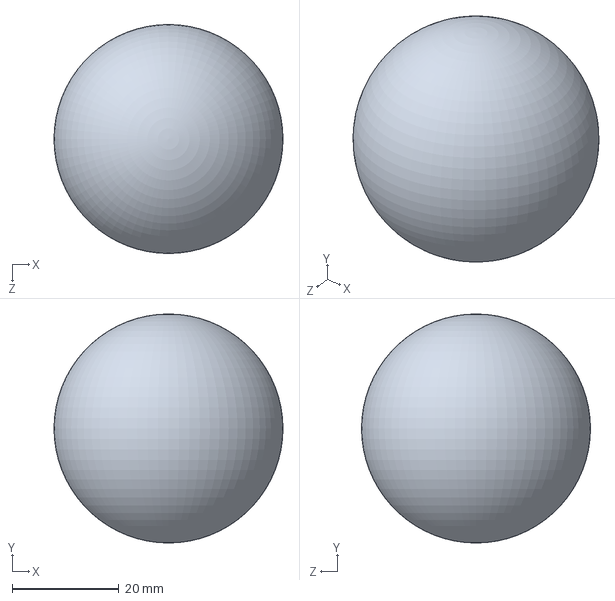
[picture p75: CAD file, 2020-06-09]
lobsta_concept_CAD/Ball Dropper/BALL.SLDPRT
43.0 x 43.0 x 43.0 mm
