uvic-auvic/Mechanical-Team/lobsta_concept_CAD/battery/XT60 Stecker.SLDPRT

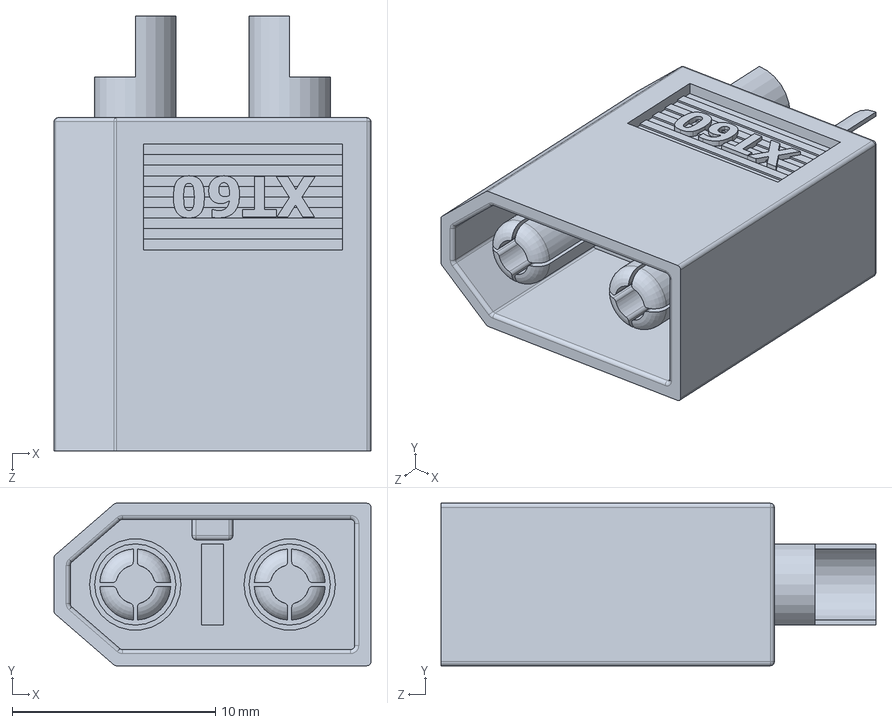
[picture p76: CAD file, 2020-03-10]
lobsta_concept_CAD/battery/XT60 Stecker.SLDPRT
15.6 x 8.00 x 21.4 mm
