uvic-auvic/Mechanical-Team/lobsta_concept_CAD/Camera Housing/auv01_camera_hull_lens_holder_dome_videoray.SLDPRT

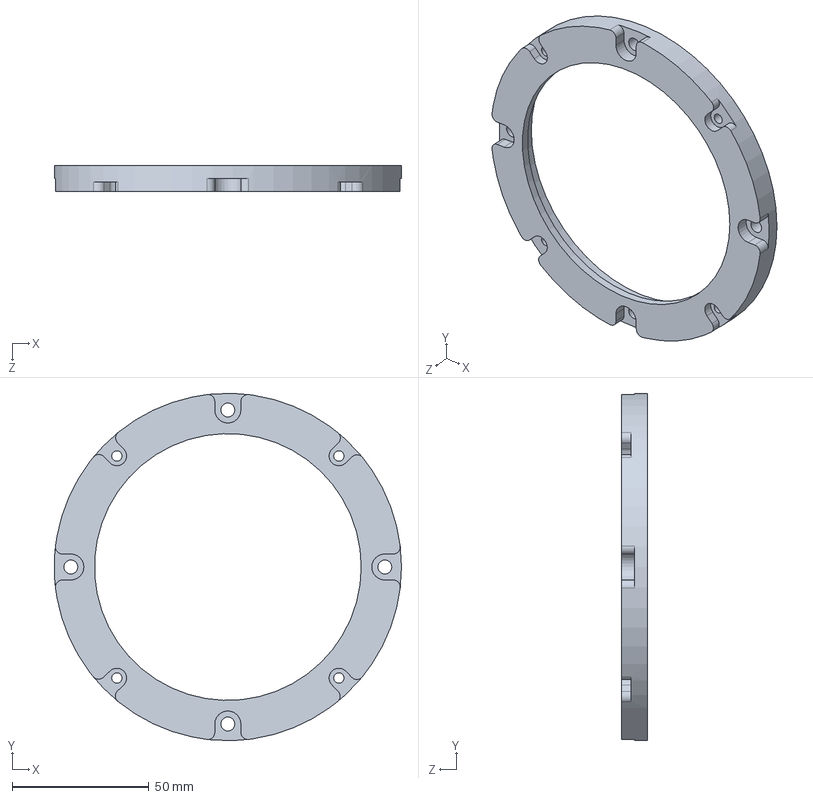
[picture p77: CAD file, 2020-03-10]
lobsta_concept_CAD/Camera Housing/auv01_camera_hull_lens_holder_dome_videoray.SLDPRT
126.9 x 126.9 x 9.53 mm
