uvic-auvic/Mechanical-Team/Mockup Drawings/square_sub/top_plate.SLDPRT

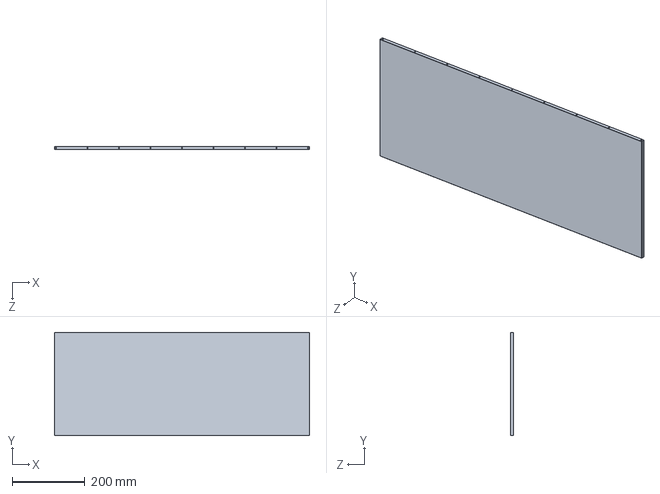
[picture p78: CAD file, 2019-10-25]
Mockup Drawings/square_sub/top_plate.SLDPRT
700.0 x 284.0 x 8.00 mm
