uvic-auvic/Mechanical-Team/Torpedos/barrel_stand.SLDPRT

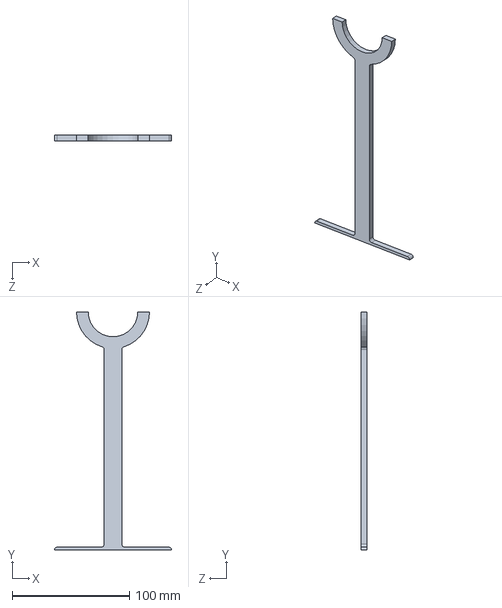
[picture p79: CAD file, 2020-06-09]
Torpedos/barrel_stand.SLDPRT
100.0 x 202.7 x 5.00 mm
