uvic-auvic/Mechanical-Team/Final Assembly_POLARIS/Attachment Detail.SLDPRT

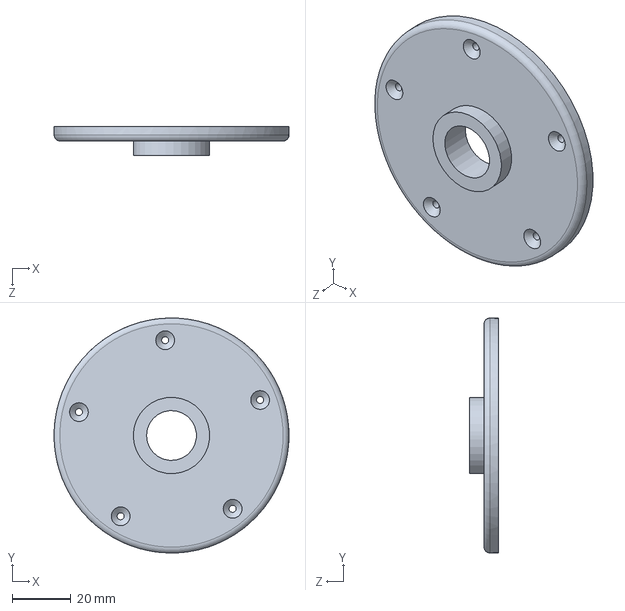
[picture p80: CAD file, 2020-06-30]
Final Assembly_POLARIS/Attachment Detail.SLDPRT
80.0 x 80.0 x 10.0 mm
