uvic-auvic/Mechanical-Team/frame/demonstration/PART_PicRail.sldprt

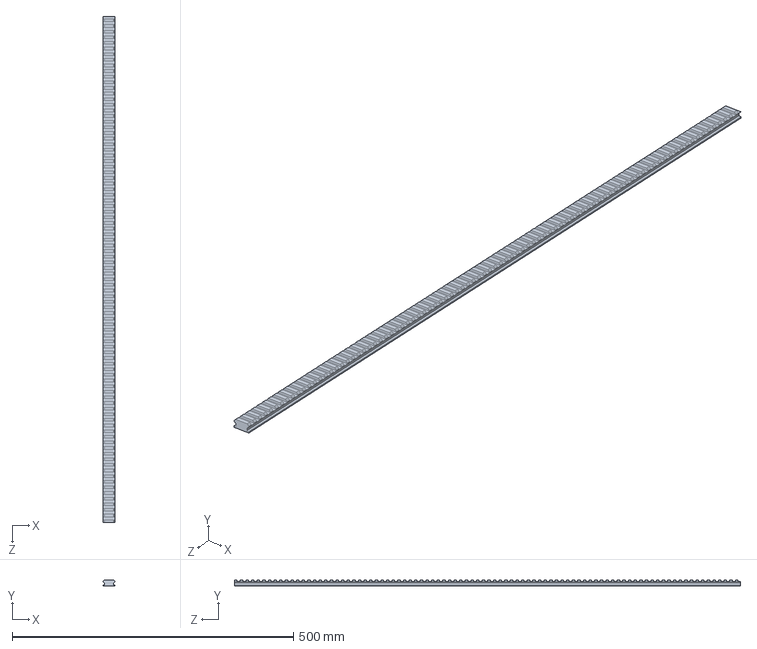
[picture p81: CAD file, 2020-06-30]
frame/demonstration/PART_PicRail.sldprt
21.2 x 11.2 x 900.0 mm
