uvic-auvic/Mechanical-Team/lobsta_concept_CAD/Camera Housing/camera_foward.SLDPRT

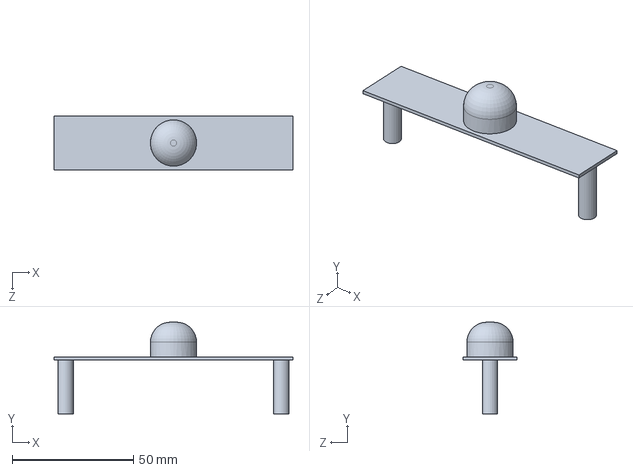
[picture p82: CAD file, 2020-03-10]
lobsta_concept_CAD/Camera Housing/camera_foward.SLDPRT
98.4 x 37.8 x 22.2 mm
