uvic-auvic/Mechanical-Team/lobsta_concept_CAD/cap.SLDPRT

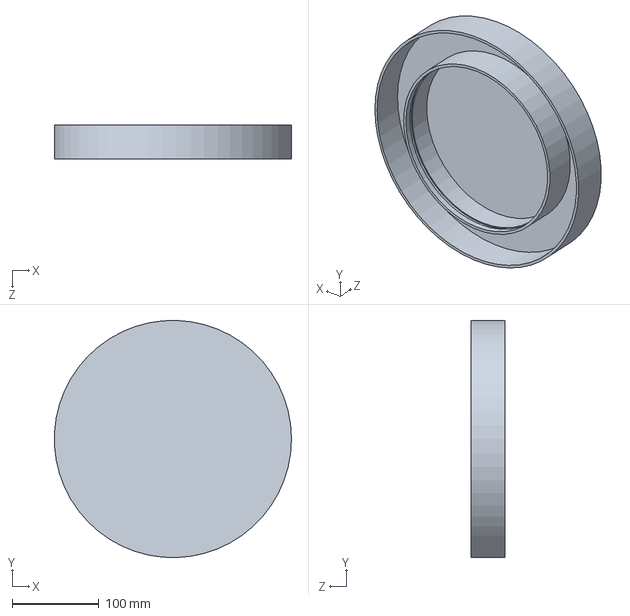
[picture p83: CAD file, 2020-01-29]
lobsta_concept_CAD/cap.SLDPRT
272.8 x 272.9 x 38.7 mm
