uvic-auvic/Mechanical-Team/Torpedos/barrel.SLDPRT

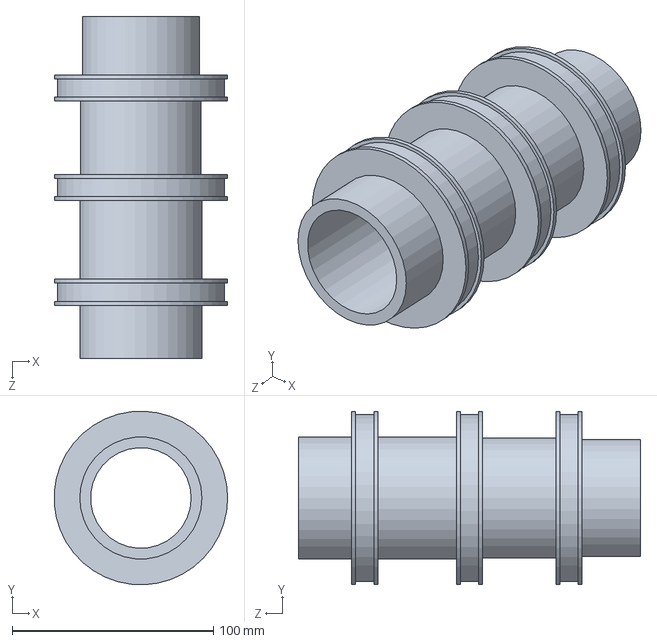
[picture p84: CAD file, 2020-06-09]
Torpedos/barrel.SLDPRT
86.2 x 86.2 x 170.0 mm
