uvic-auvic/Mechanical-Team/frame/demonstration/TCH-500-1335802.SLDPRT

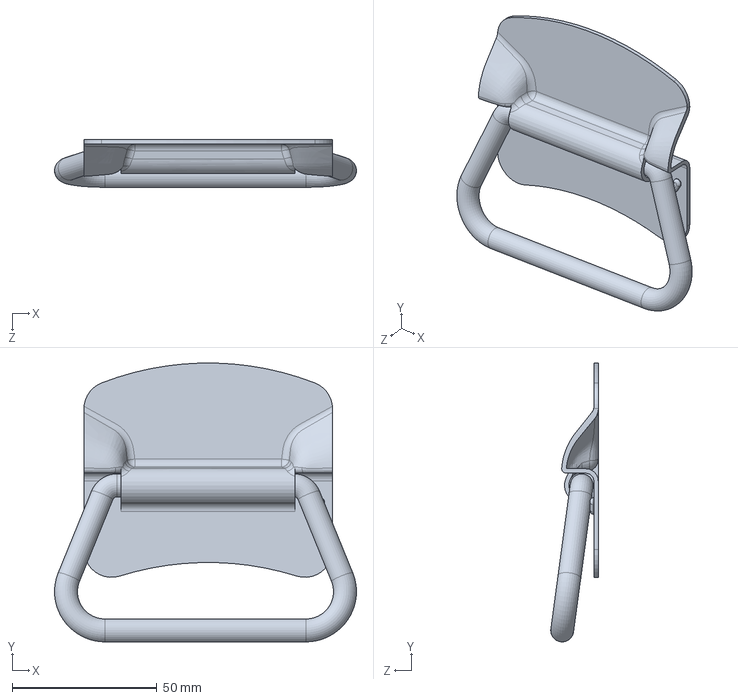
[picture p85: CAD file, 2020-06-30]
frame/demonstration/TCH-500-1335802.SLDPRT
104.1 x 96.1 x 16.4 mm
