uvic-auvic/Mechanical-Team/lobsta_concept_CAD/Camera Housing/Test Camera (2).SLDPRT

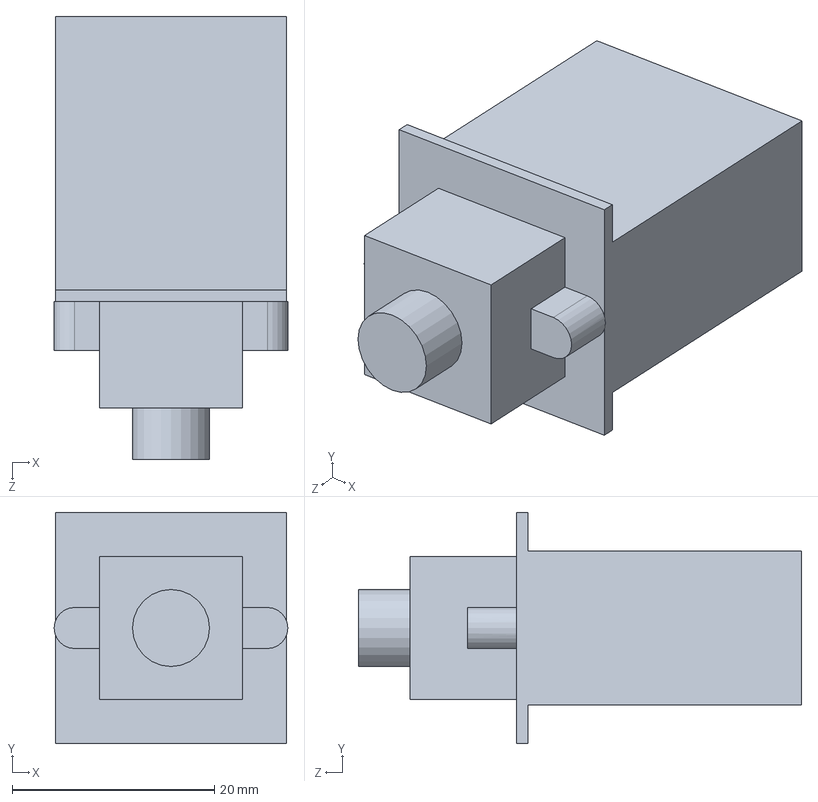
[picture p86: CAD file, 2020-03-10]
lobsta_concept_CAD/Camera Housing/Test Camera (2).SLDPRT
23.1 x 22.9 x 43.8 mm
