uvic-auvic/Mechanical-Team/Torpedos/solenoid_springstopper.SLDPRT

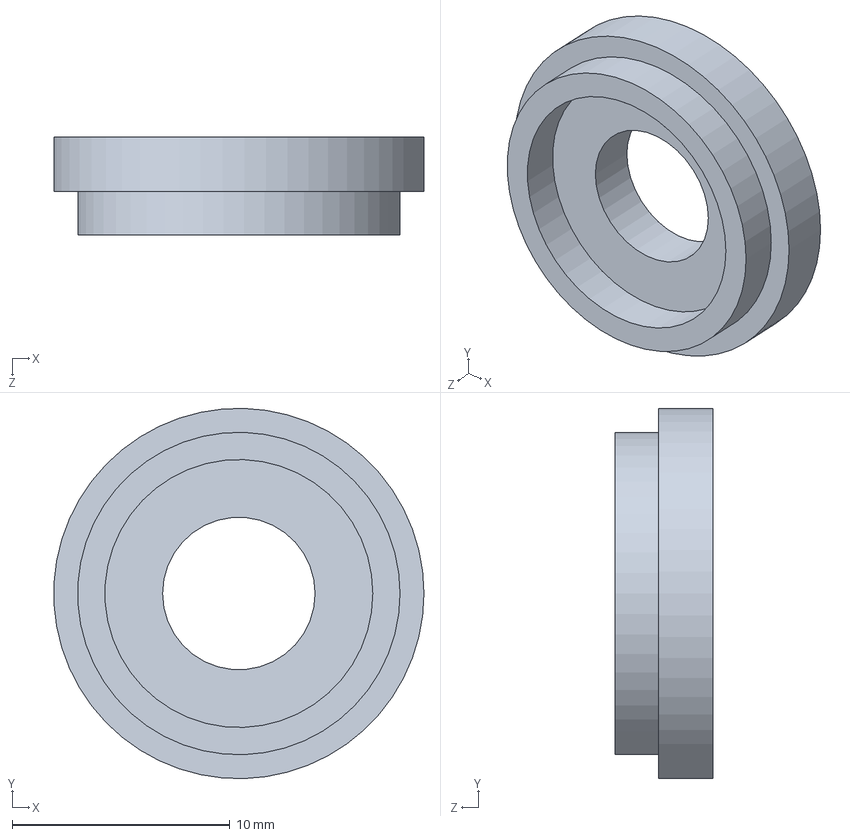
[picture p87: CAD file, 2020-03-18]
Torpedos/solenoid_springstopper.SLDPRT
17.0 x 17.0 x 4.50 mm
