uvic-auvic/Mechanical-Team/Final Assembly_POLARIS/Clutch.SLDPRT

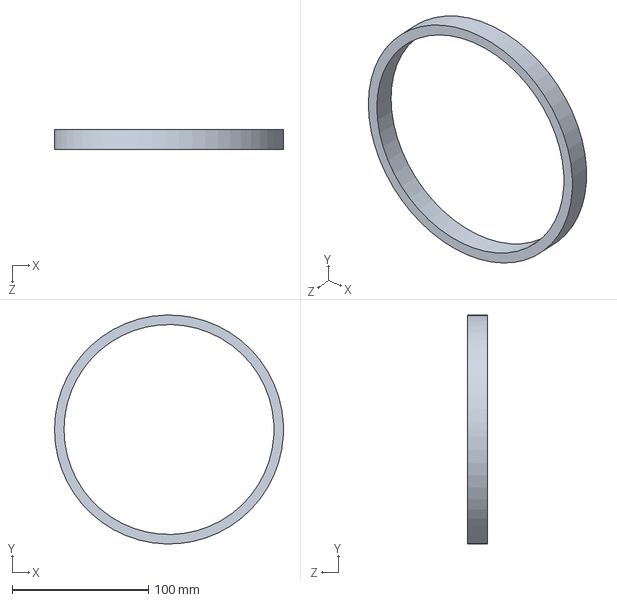
[picture p88: CAD file, 2020-06-30]
Final Assembly_POLARIS/Clutch.SLDPRT
168.0 x 167.9 x 15.0 mm
