uvic-auvic/Mechanical-Team/Final Assembly_POLARIS/shaftMECH360.SLDPRT

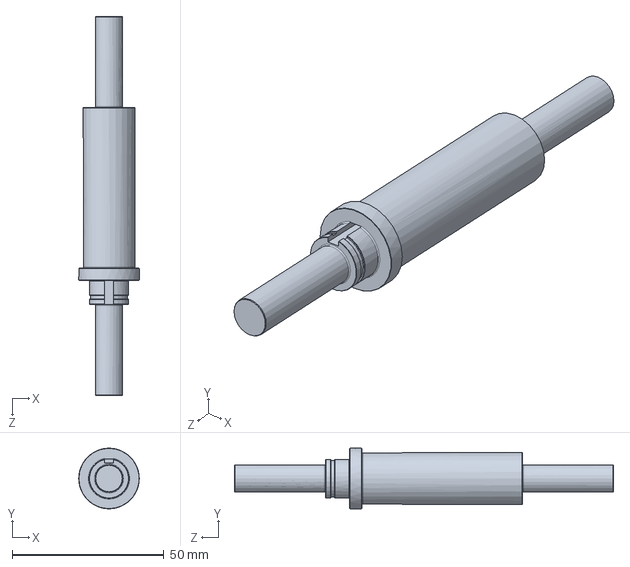
[picture p89: CAD file, 2020-06-30]
Final Assembly_POLARIS/shaftMECH360.SLDPRT
20.0 x 20.0 x 125.0 mm
