uvic-auvic/Mechanical-Team/lobsta_concept_CAD/auv_assemblies/Mirrorside_plate.sldprt

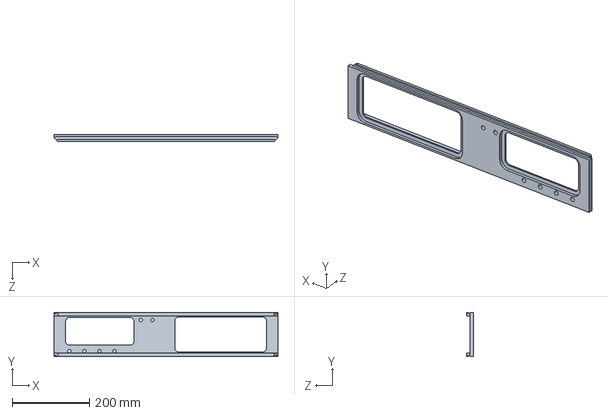
[picture p90: CAD file, 2020-05-26]
lobsta_concept_CAD/auv_assemblies/Mirrorside_plate.sldprt
581.0 x 115.0 x 19.0 mm
