uvic-auvic/Mechanical-Team/lobsta_concept_CAD/Camera Housing/Bottom Facing Camera Adapter.SLDPRT

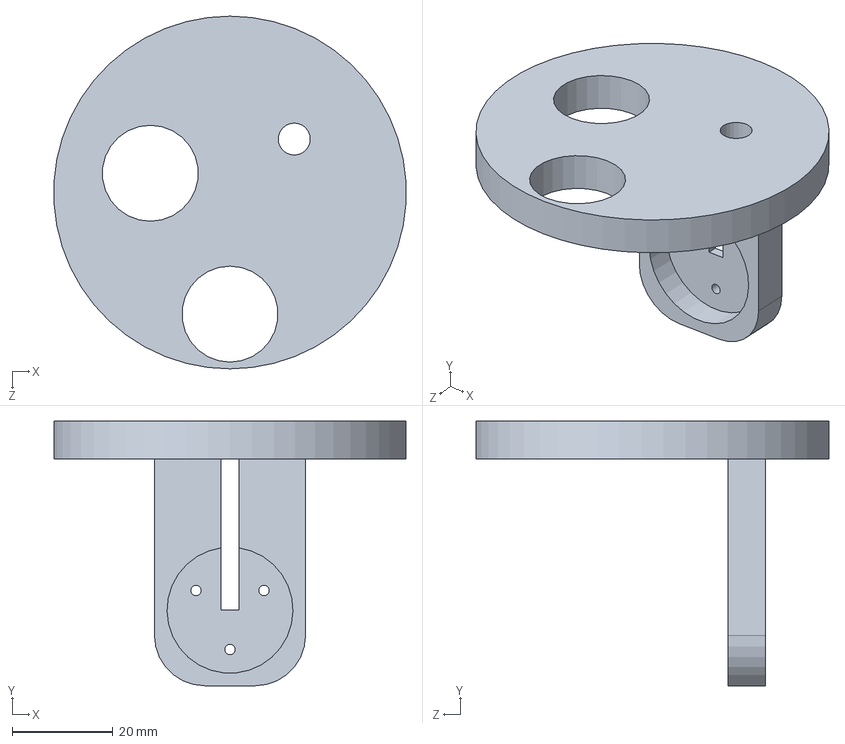
[picture p91: CAD file, 2020-03-10]
lobsta_concept_CAD/Camera Housing/Bottom Facing Camera Adapter.SLDPRT
69.9 x 52.5 x 70.0 mm
