uvic-auvic/Mechanical-Team/lobsta_concept_CAD/flat_frame.SLDPRT

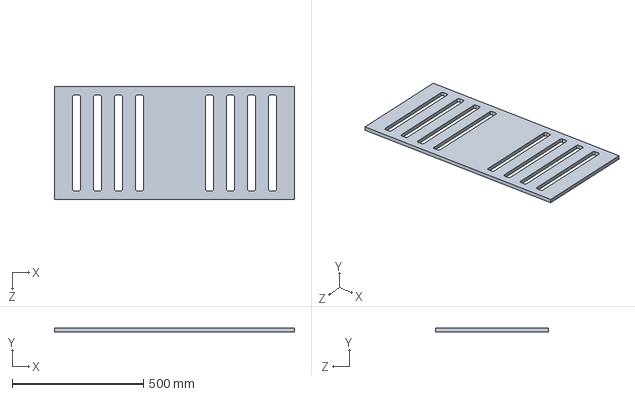
[picture p92: CAD file, 2020-01-28]
lobsta_concept_CAD/flat_frame.SLDPRT
914.0 x 15.0 x 430.0 mm
