uvic-auvic/Mechanical-Team/lobsta_concept_CAD/side_frame.SLDPRT

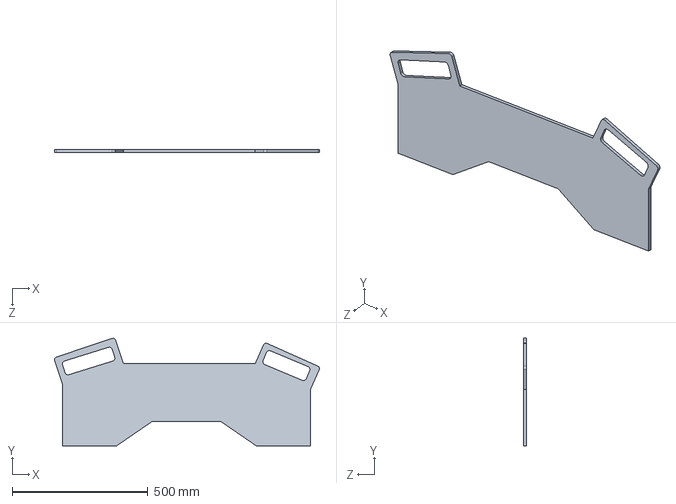
[picture p93: CAD file, 2020-01-28]
lobsta_concept_CAD/side_frame.SLDPRT
976.9 x 396.4 x 10.0 mm
