uvic-auvic/Mechanical-Team/lobsta_concept_CAD/Camera Housing/auv01_camera_dome_videoray.SLDPRT

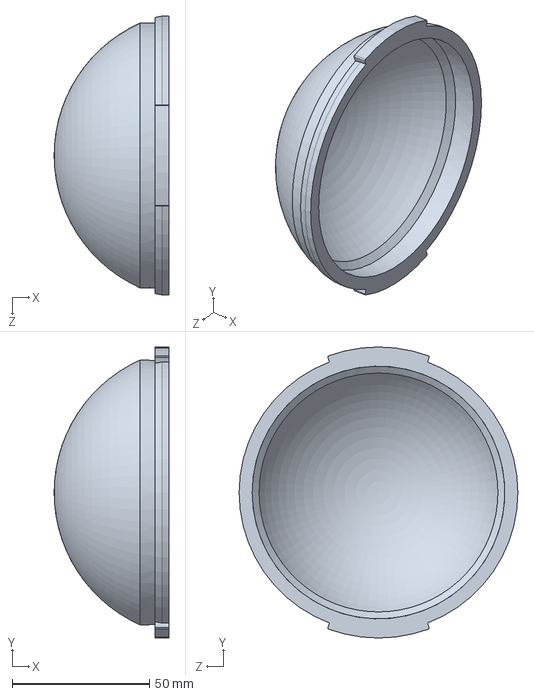
[picture p94: CAD file, 2020-03-10]
lobsta_concept_CAD/Camera Housing/auv01_camera_dome_videoray.SLDPRT
41.8 x 106.1 x 101.6 mm
