uvic-auvic/Mechanical-Team/lobsta_concept_CAD/Motor Shell.SLDPRT

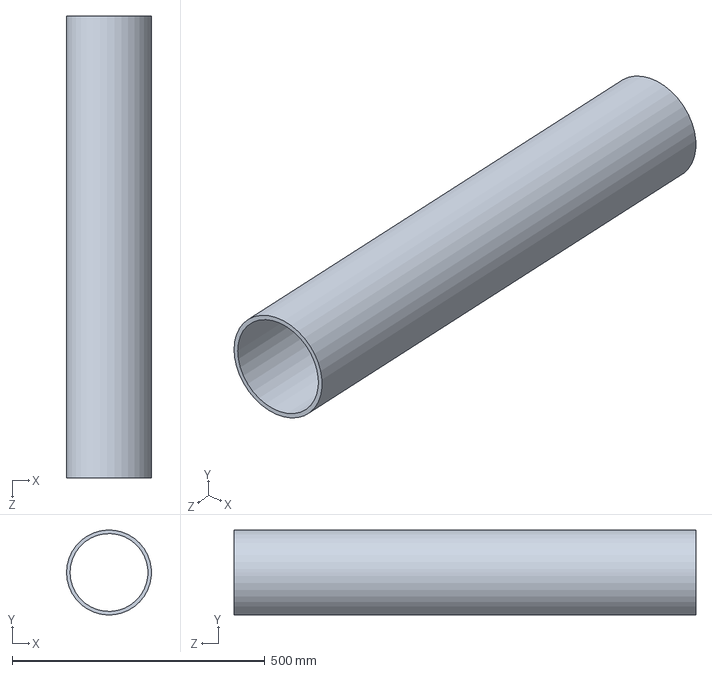
[picture p95: CAD file, 2020-01-28]
lobsta_concept_CAD/Motor Shell.SLDPRT
168.3 x 168.1 x 914.4 mm
