uvic-auvic/Mechanical-Team/Final Assembly_POLARIS/Sun_bearing.SLDPRT

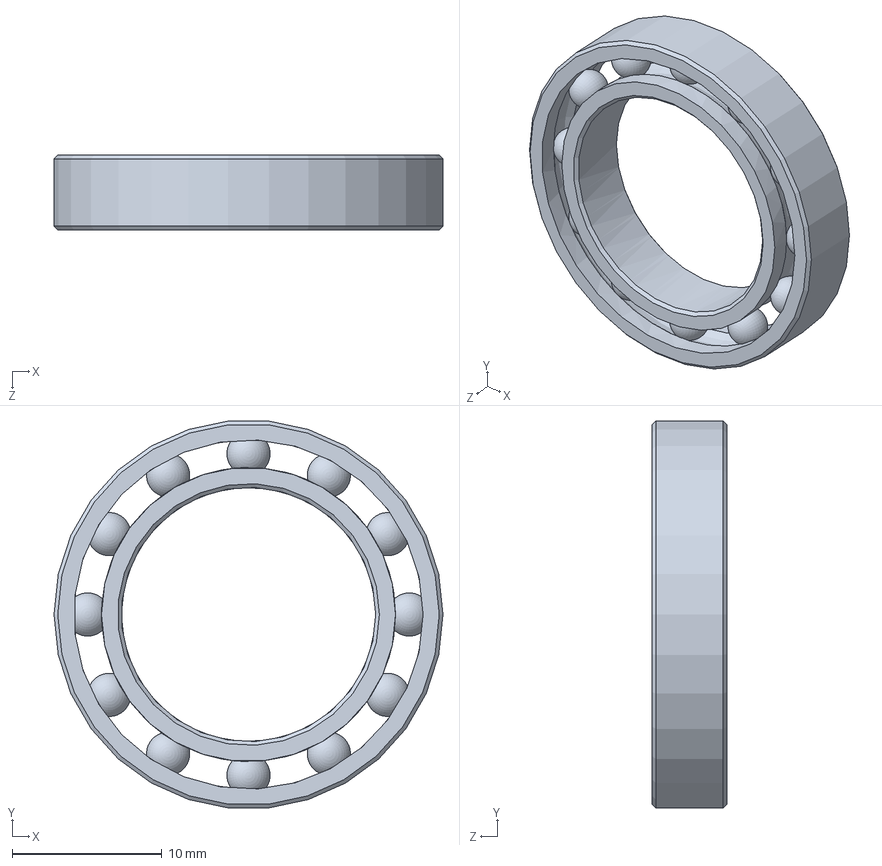
[picture p96: CAD file, 2020-06-30]
Final Assembly_POLARIS/Sun_bearing.SLDPRT
26.0 x 25.9 x 5.00 mm
