uvic-auvic/Mechanical-Team/lobsta_concept_CAD/auv_assemblies/lid_rectangular_bottom.sldprt

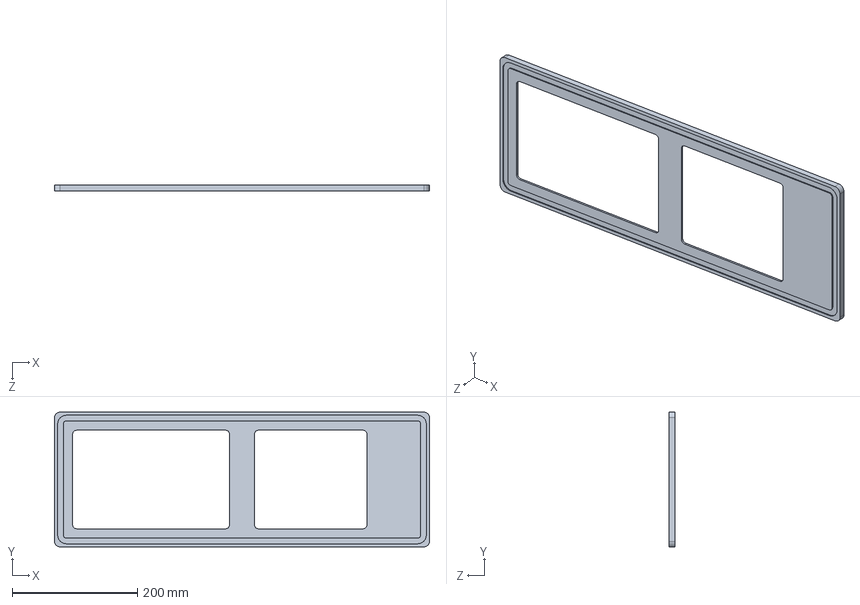
[picture p97: CAD file, 2020-03-20]
lobsta_concept_CAD/auv_assemblies/lid_rectangular_bottom.sldprt
599.0 x 215.4 x 9.00 mm
