uvic-auvic/Mechanical-Team/Final Assembly_POLARIS/Sun Gear.SLDPRT

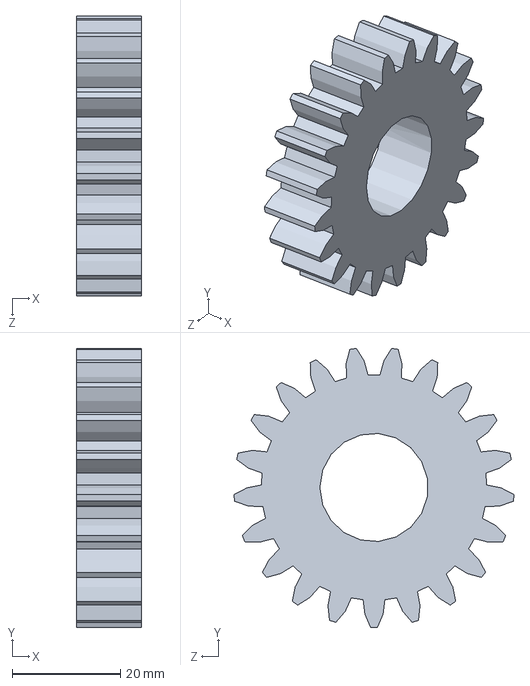
[picture p98: CAD file, 2020-06-30]
Final Assembly_POLARIS/Sun Gear.SLDPRT
12.0 x 51.5 x 51.7 mm
