uvic-auvic/Mechanical-Team/lobsta_concept_CAD/auv_assemblies/side_window_small.sldprt

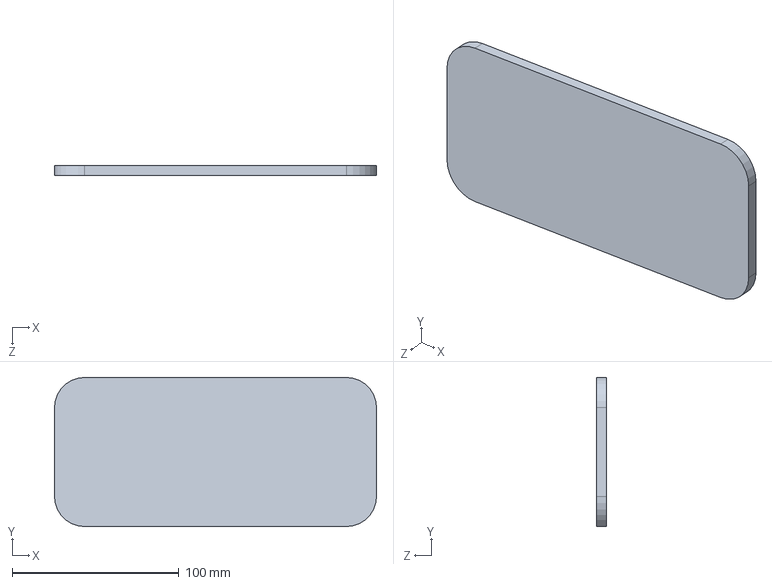
[picture p99: CAD file, 2020-03-20]
lobsta_concept_CAD/auv_assemblies/side_window_small.sldprt
193.4 x 89.5 x 6.00 mm
