uvic-auvic/Mechanical-Team/Final Assembly_POLARIS/Motor_cover.SLDPRT

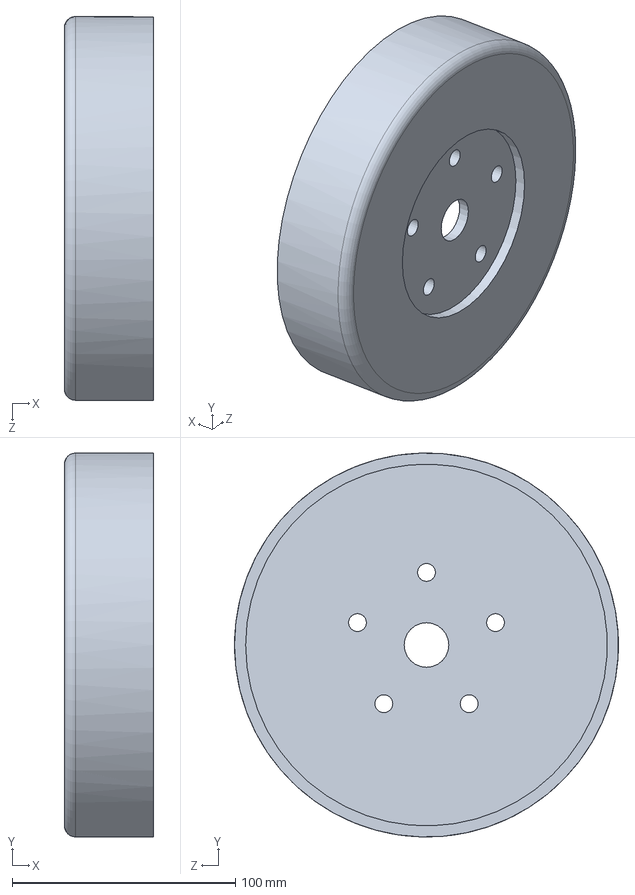
[picture p100: CAD file, 2020-06-30]
Final Assembly_POLARIS/Motor_cover.SLDPRT
40.0 x 172.0 x 172.0 mm
