uvic-auvic/Mechanical-Team/Final Assembly_POLARIS/Key.SLDPRT

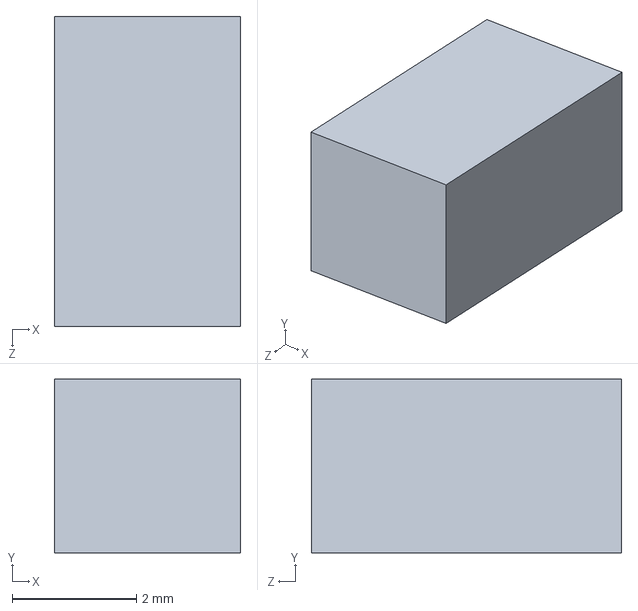
[picture p101: CAD file, 2020-06-30]
Final Assembly_POLARIS/Key.SLDPRT
3.00 x 2.80 x 5.00 mm
