uvic-auvic/Mechanical-Team/lobsta_concept_CAD/auv_assemblies/lid_rectangular.sldprt

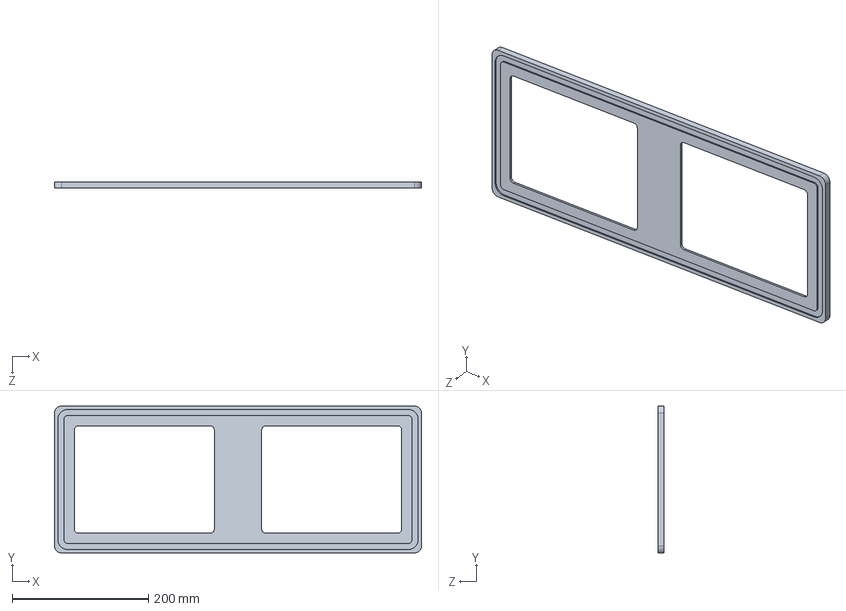
[picture p102: CAD file, 2020-03-18]
lobsta_concept_CAD/auv_assemblies/lid_rectangular.sldprt
538.7 x 215.4 x 9.00 mm
