uvic-auvic/Mechanical-Team/Final Assembly_POLARIS/Planet 26t.SLDPRT

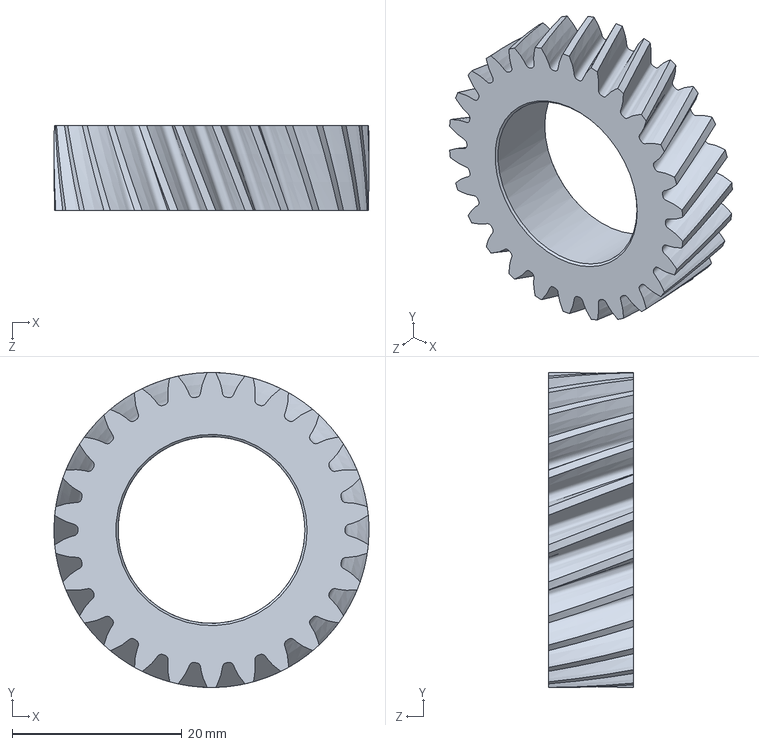
[picture p103: CAD file, 2020-06-30]
Final Assembly_POLARIS/Planet 26t.SLDPRT
37.1 x 37.1 x 10.0 mm
