uvic-auvic/Mechanical-Team/lobsta_concept_CAD/auv_assemblies/barstock support_short.SLDPRT

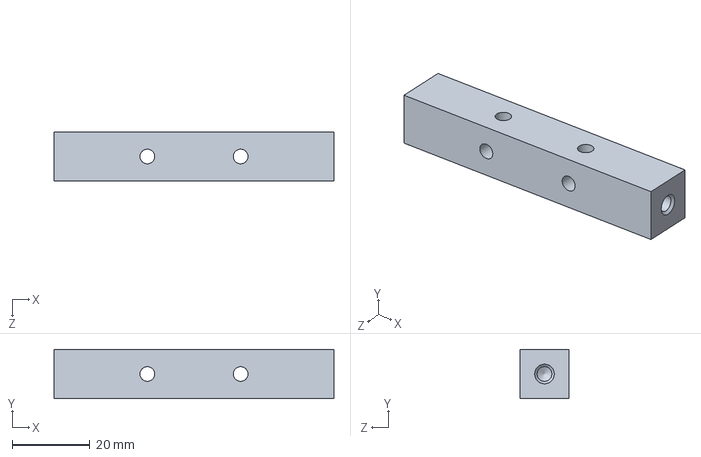
[picture p104: CAD file, 2020-03-18]
lobsta_concept_CAD/auv_assemblies/barstock support_short.SLDPRT
72.0 x 12.7 x 12.7 mm
