uvic-auvic/Mechanical-Team/Final Assembly_POLARIS/Motor_cover_rev1.SLDPRT

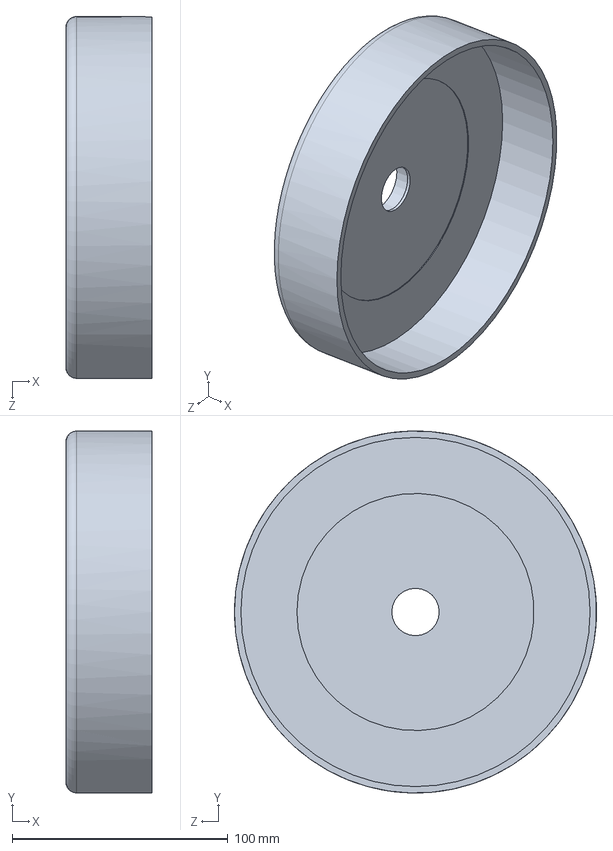
[picture p105: CAD file, 2020-06-30]
Final Assembly_POLARIS/Motor_cover_rev1.SLDPRT
40.0 x 168.0 x 168.0 mm
