uvic-auvic/Mechanical-Team/Final Assembly_POLARIS/Planet 28t.SLDPRT

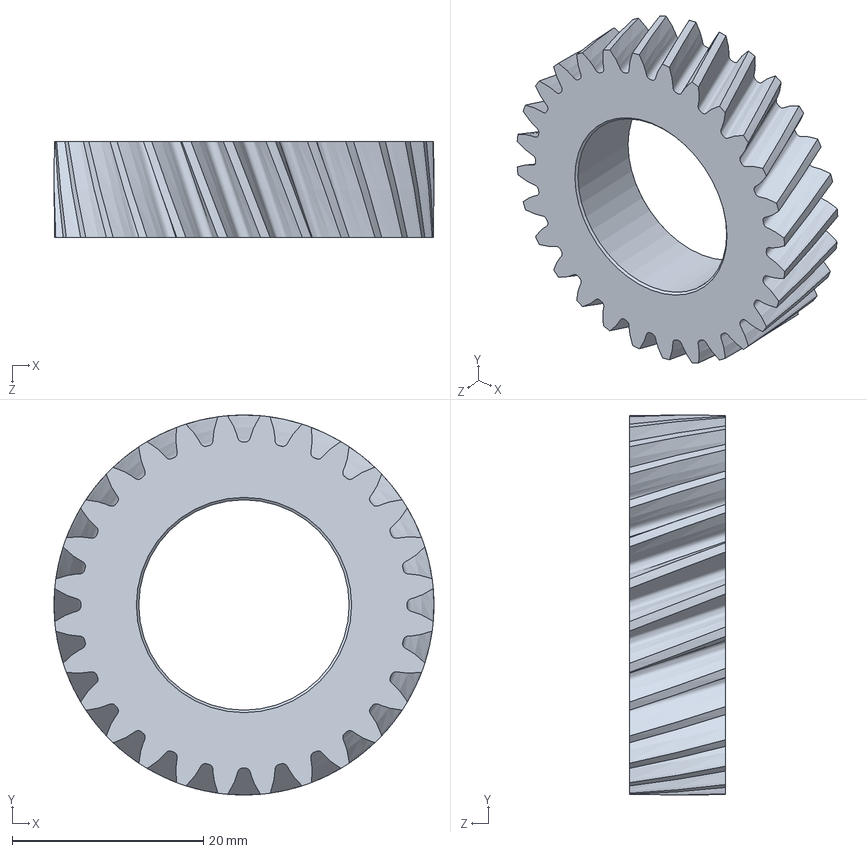
[picture p106: CAD file, 2020-06-30]
Final Assembly_POLARIS/Planet 28t.SLDPRT
39.7 x 39.7 x 10.0 mm
