uvic-auvic/Mechanical-Team/lobsta_concept_CAD/auv_assemblies/rear_plate.sldprt

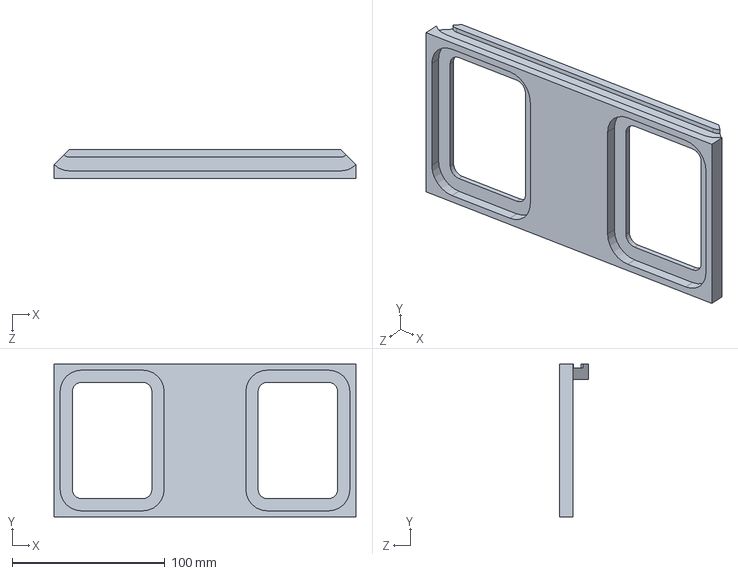
[picture p107: CAD file, 2020-03-18]
lobsta_concept_CAD/auv_assemblies/rear_plate.sldprt
197.4 x 100.0 x 19.0 mm
