uvic-auvic/Mechanical-Team/Final Assembly_POLARIS/Motor_Rotor.SLDPRT

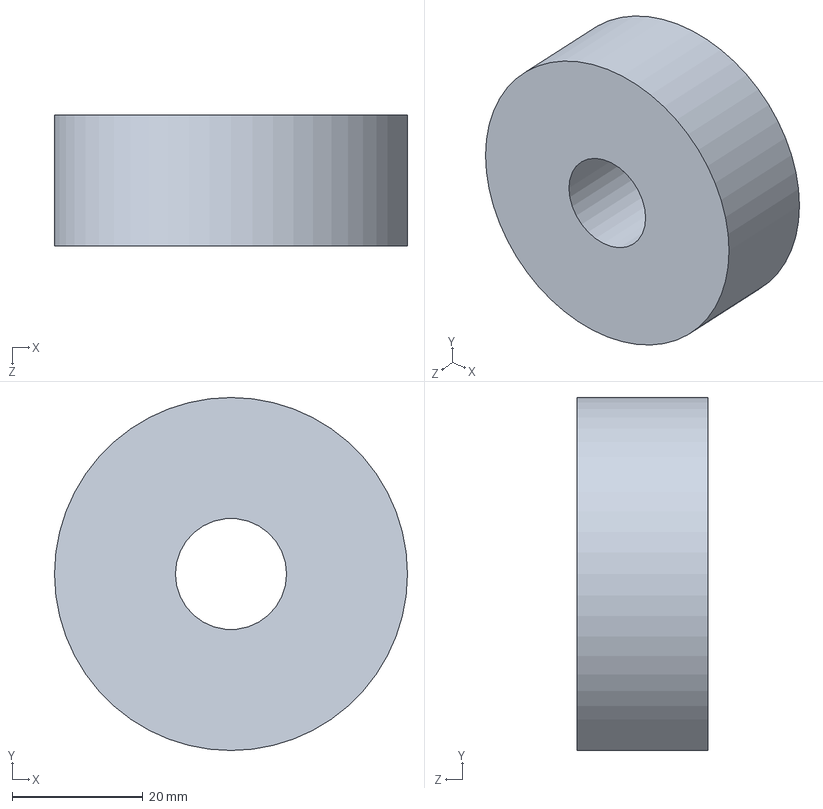
[picture p108: CAD file, 2020-06-30]
Final Assembly_POLARIS/Motor_Rotor.SLDPRT
54.0 x 54.0 x 20.0 mm
