uvic-auvic/Mechanical-Team/lobsta_concept_CAD/auv_assemblies/front_plate.sldprt

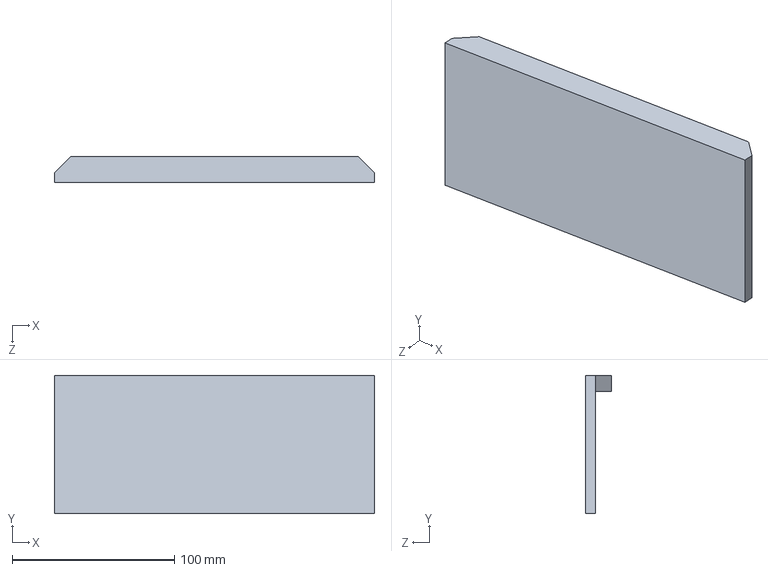
[picture p109: CAD file, 2020-03-18]
lobsta_concept_CAD/auv_assemblies/front_plate.sldprt
197.4 x 85.2 x 16.0 mm
