uvic-auvic/Mechanical-Team/Final Assembly_POLARIS/Planet_ClipRing.SLDPRT

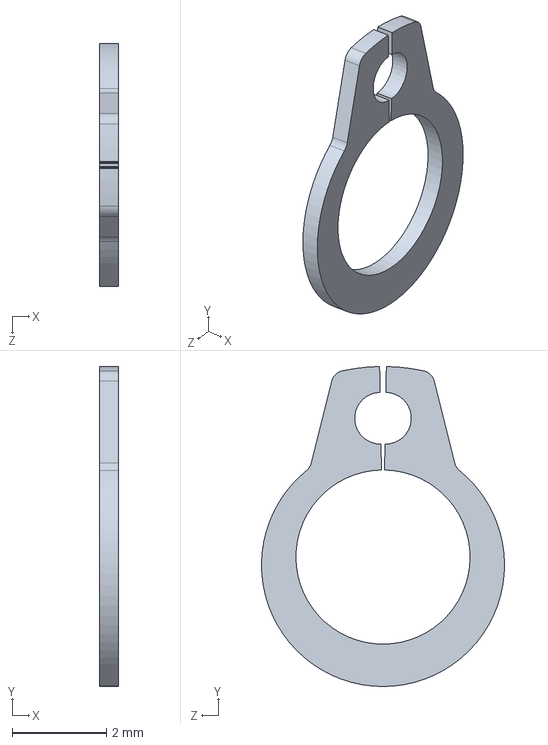
[picture p110: CAD file, 2020-06-30]
Final Assembly_POLARIS/Planet_ClipRing.SLDPRT
0.4 x 6.80 x 5.16 mm
