uvic-auvic/Mechanical-Team/lobsta_concept_CAD/auv_assemblies/side_plate.sldprt

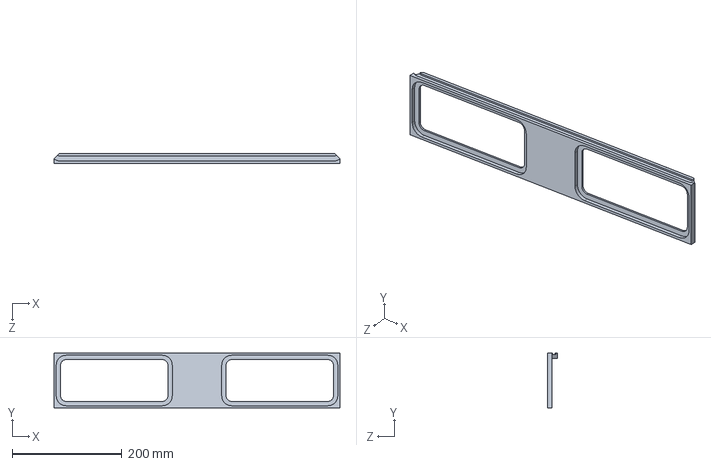
[picture p111: CAD file, 2020-03-18]
lobsta_concept_CAD/auv_assemblies/side_plate.sldprt
520.7 x 100.0 x 19.0 mm
