uvic-auvic/Mechanical-Team/Final Assembly_POLARIS/End Cap.SLDPRT

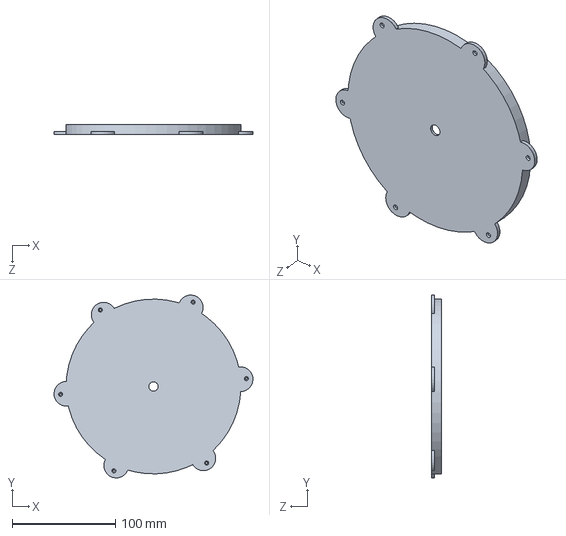
[picture p112: CAD file, 2020-06-30]
Final Assembly_POLARIS/End Cap.SLDPRT
192.4 x 176.9 x 10.0 mm
