uvic-auvic/Mechanical-Team/Final Assembly_POLARIS/Carrier.SLDPRT

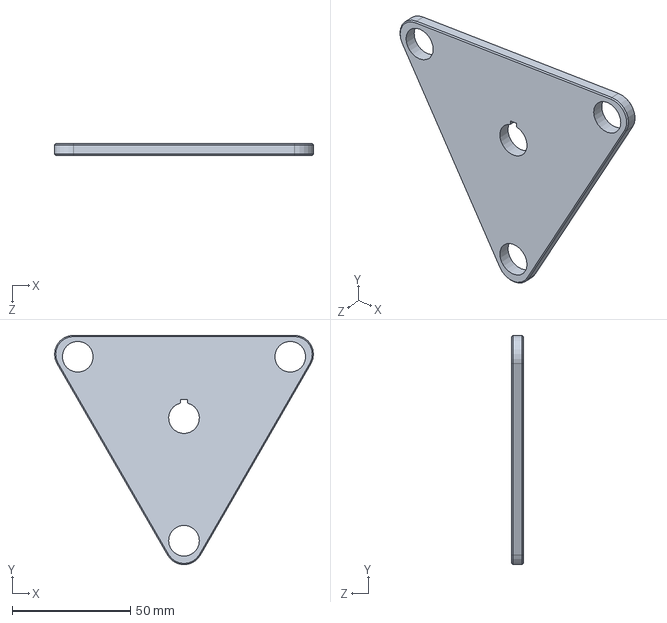
[picture p113: CAD file, 2020-06-30]
Final Assembly_POLARIS/Carrier.SLDPRT
109.5 x 97.0 x 5.00 mm
