uvic-auvic/Mechanical-Team/lobsta_concept_CAD/auv_assemblies/barstock support_long.SLDPRT

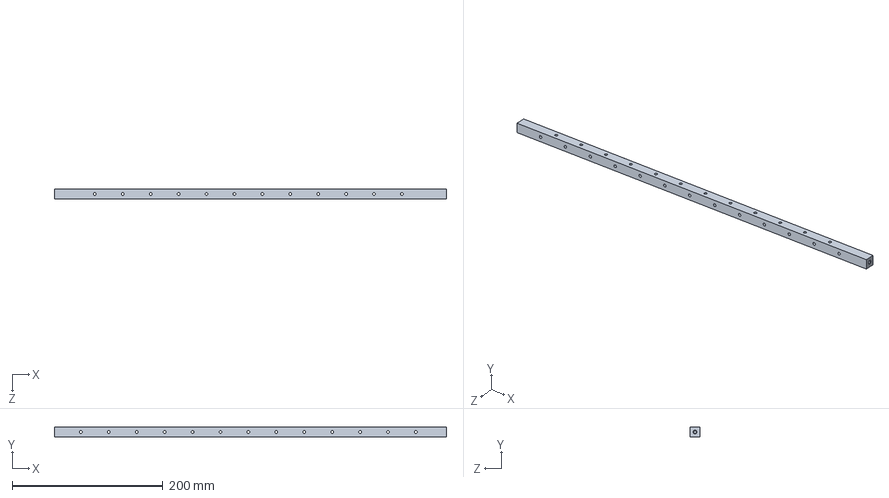
[picture p114: CAD file, 2020-03-11]
lobsta_concept_CAD/auv_assemblies/barstock support_long.SLDPRT
520.7 x 12.7 x 12.7 mm
