uvic-auvic/Mechanical-Team/Final Assembly_POLARIS/Motor_circuit_board.SLDPRT

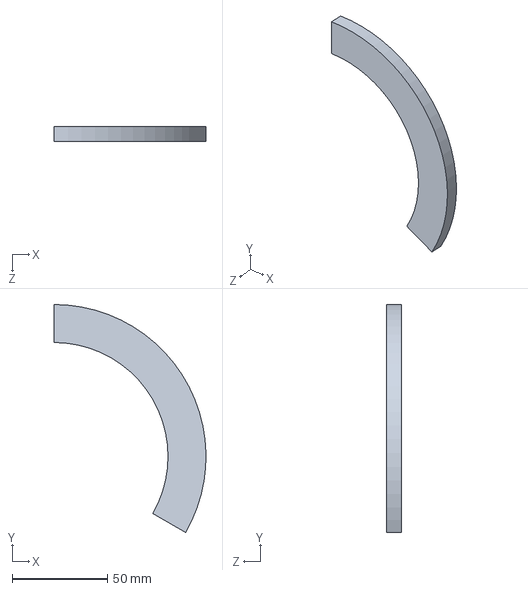
[picture p115: CAD file, 2020-06-30]
Final Assembly_POLARIS/Motor_circuit_board.SLDPRT
80.0 x 120.0 x 8.00 mm
