uvic-auvic/Mechanical-Team/Final Assembly_POLARIS/Planet Bearing.SLDPRT

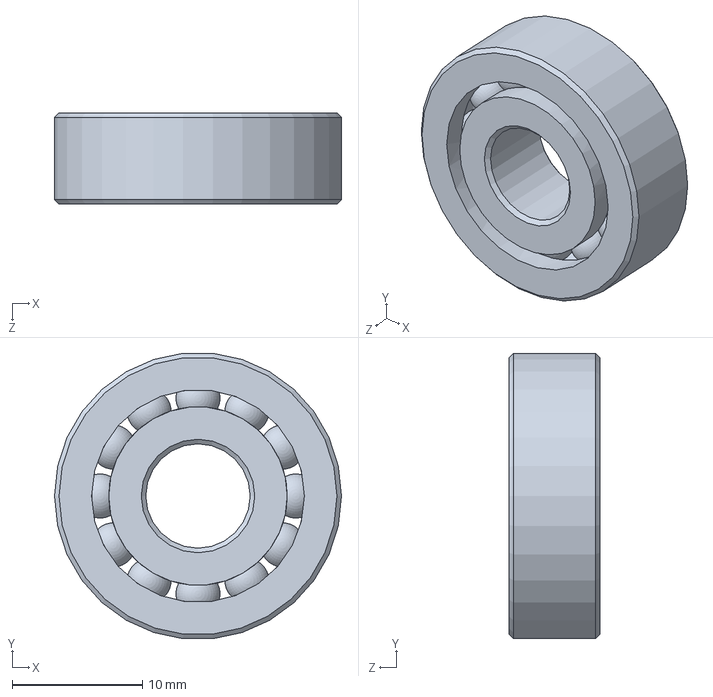
[picture p116: CAD file, 2020-06-30]
Final Assembly_POLARIS/Planet Bearing.SLDPRT
22.0 x 21.9 x 7.00 mm
