uvic-auvic/Mechanical-Team/Final Assembly_POLARIS/Retaining Ring.SLDPRT

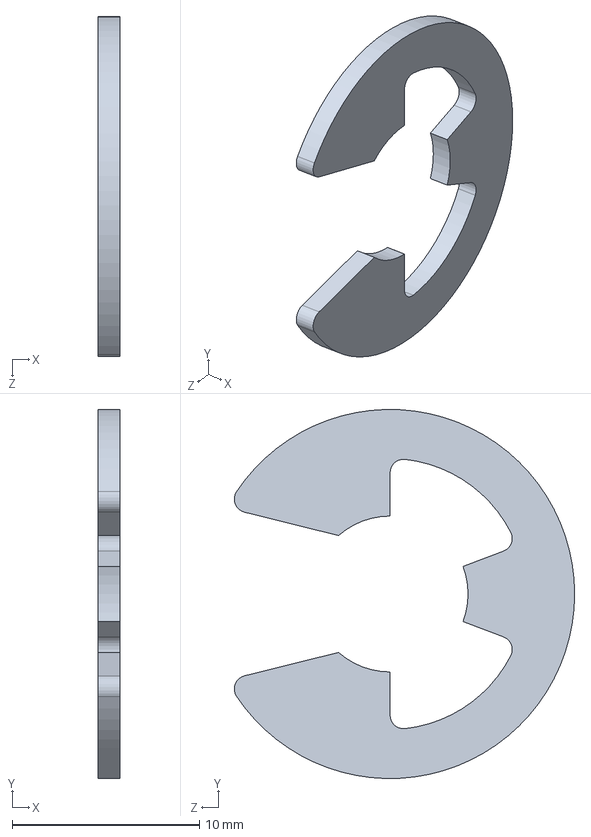
[picture p117: CAD file, 2020-06-30]
Final Assembly_POLARIS/Retaining Ring.SLDPRT
1.20 x 19.7 x 18.2 mm
