uvic-auvic/Mechanical-Team/Final Assembly_POLARIS/Ring Gear.SLDPRT

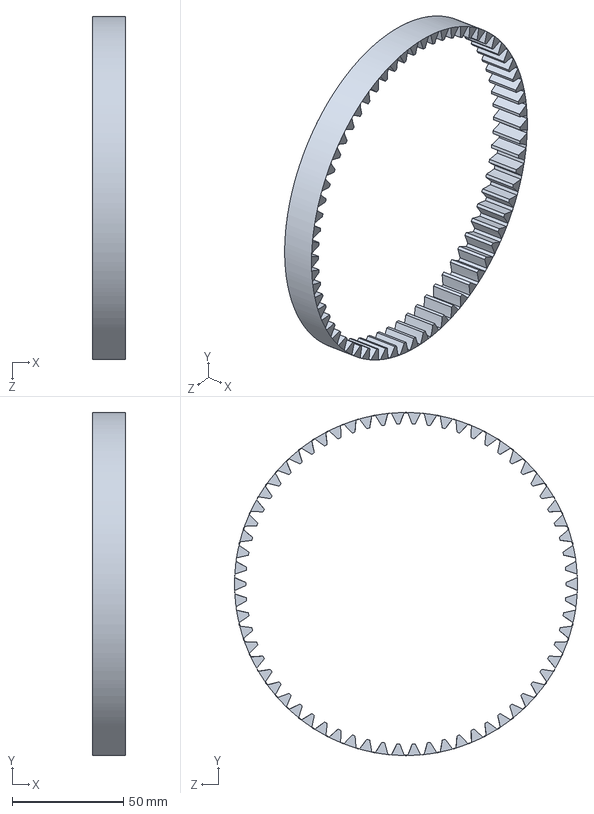
[picture p118: CAD file, 2020-06-30]
Final Assembly_POLARIS/Ring Gear.SLDPRT
15.0 x 154.2 x 154.2 mm
