uvic-auvic/Mechanical-Team/Final Assembly_POLARIS/Planet Gear.SLDPRT

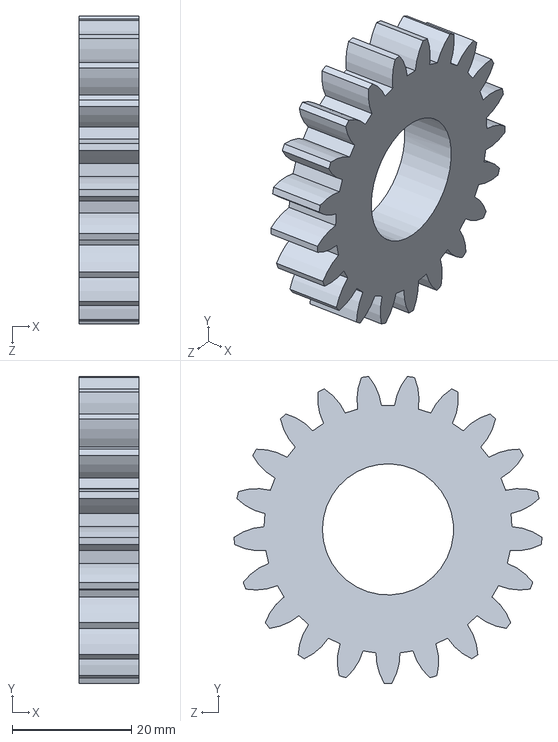
[picture p119: CAD file, 2020-06-30]
Final Assembly_POLARIS/Planet Gear.SLDPRT
10.0 x 51.5 x 51.7 mm
