uvic-auvic/Mechanical-Team/Final Assembly_POLARIS/Planet 27t.SLDPRT

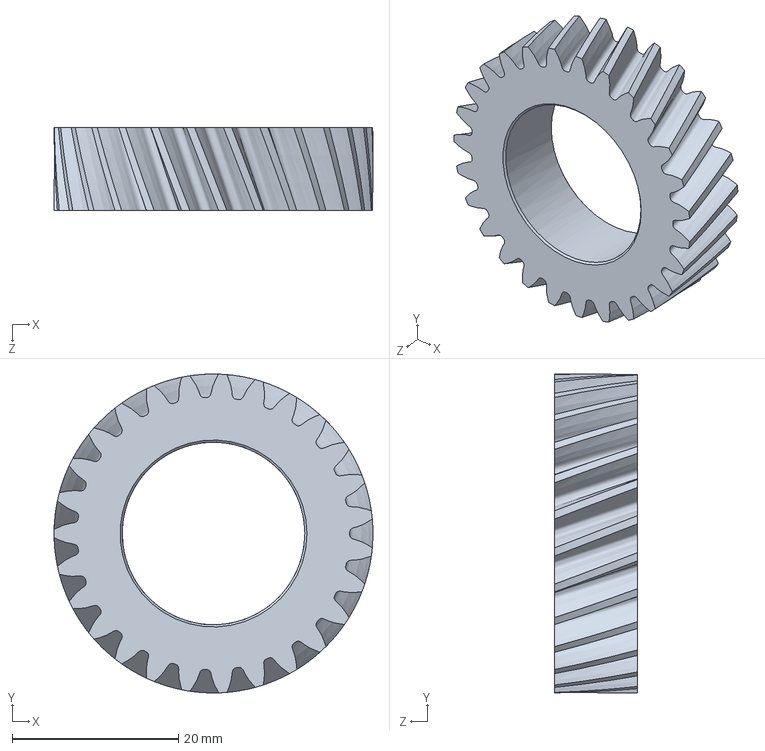
[picture p120: CAD file, 2020-06-30]
Final Assembly_POLARIS/Planet 27t.SLDPRT
38.4 x 38.4 x 10.0 mm
