uvic-auvic/Mechanical-Team/Final Assembly_POLARIS/Motor_Rotor_rev1.SLDPRT

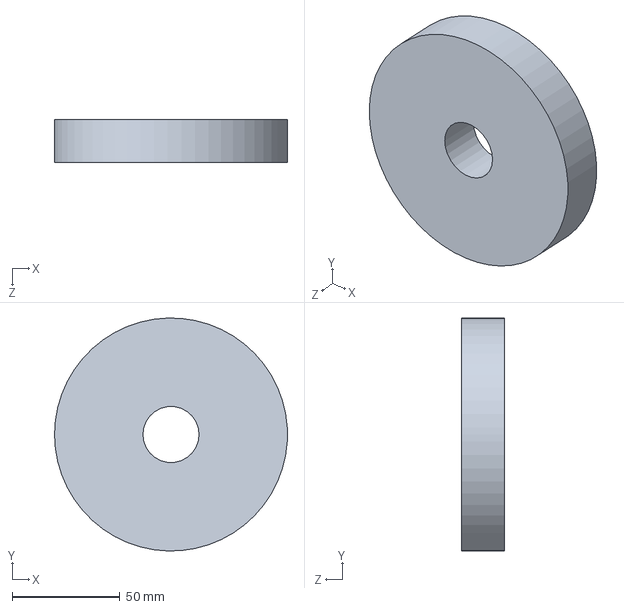
[picture p121: CAD file, 2020-06-30]
Final Assembly_POLARIS/Motor_Rotor_rev1.SLDPRT
108.0 x 108.0 x 20.0 mm
